kharper55/soundSteering_CAD_FINAL/Ultrasonic Sound Steering - Driver Rev. C/otherStuff/fab/UltrasonicDrive-B_Silkscreen.pdf

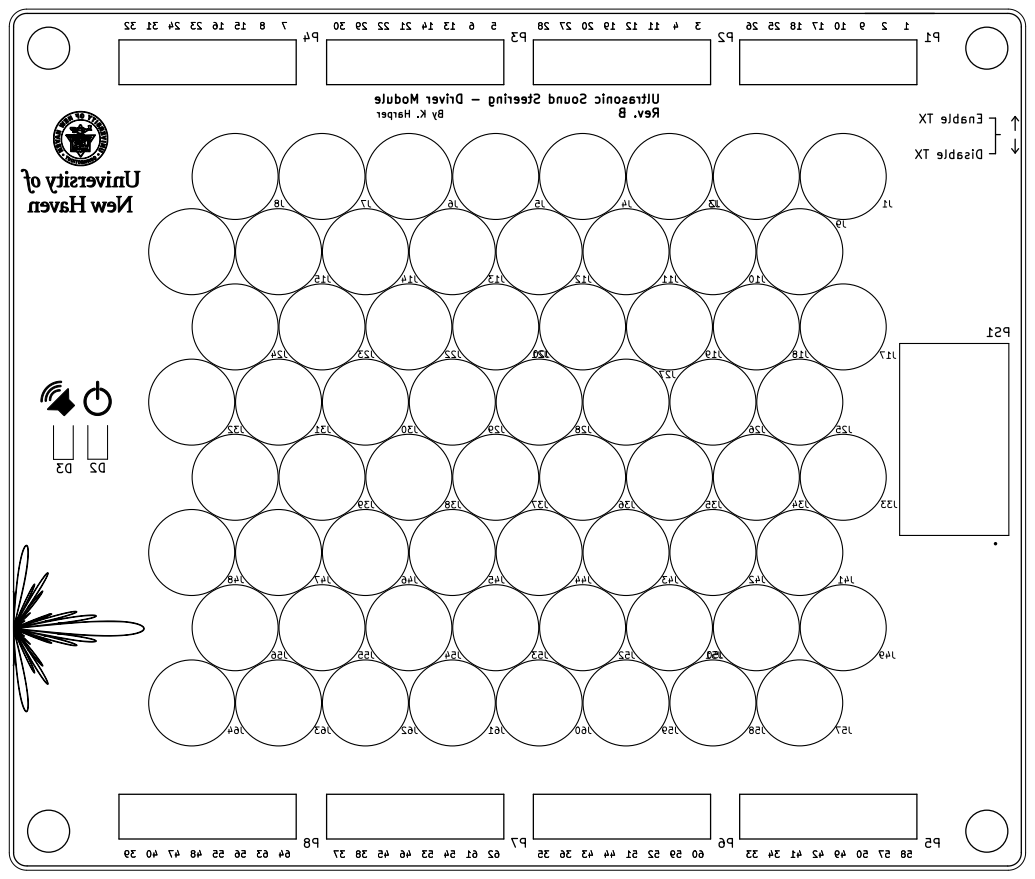
[picture p4: page 1]

15 11 By K. Harper Ultrasonic Sound Steering - Driver Module Rev. B
