kharper55/soundSteering_CAD_FINAL/Ultrasonic Sound Steering - Driver Rev. C/otherStuff/fab/UltrasonicDrive-F_Silkscreen.pdf

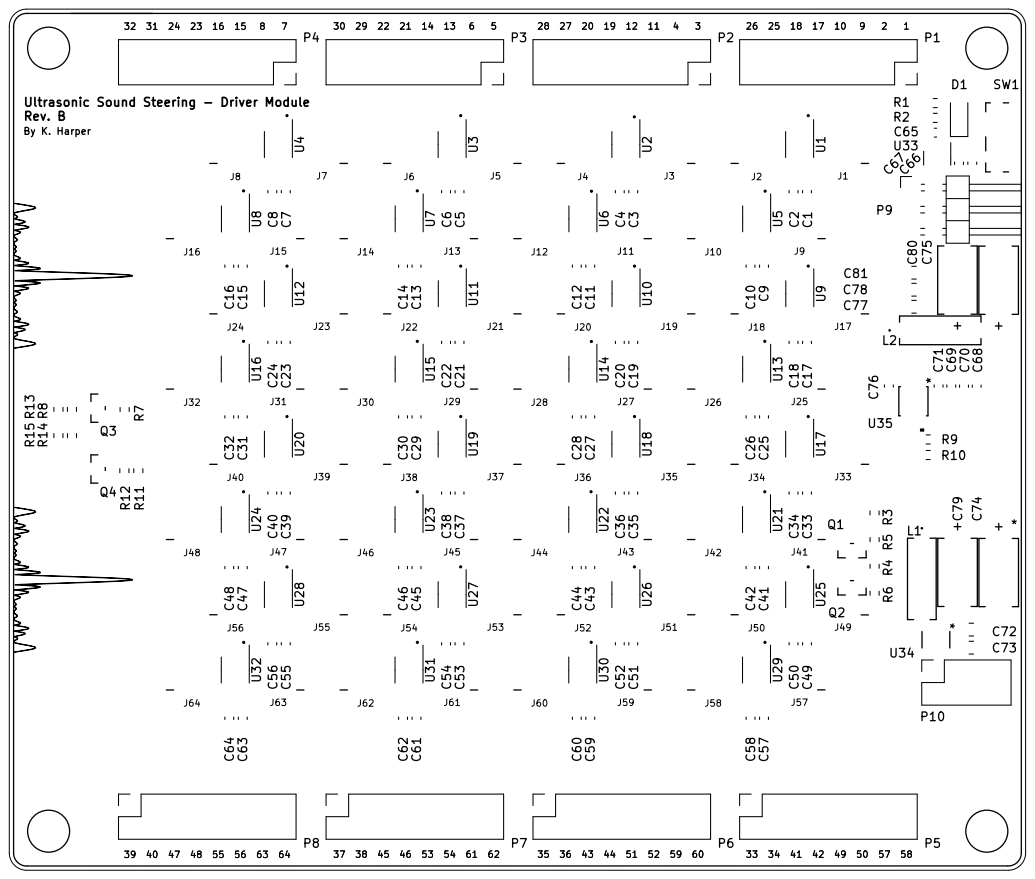
[picture p5: page 1]

30 Ultrasonic Sound Steering - Driver Module Rev. B
