kharper55/soundSteering_CAD_FINAL/Ultrasonic Sound Steering - Driver Rev. C/otherStuff/layers.pdf

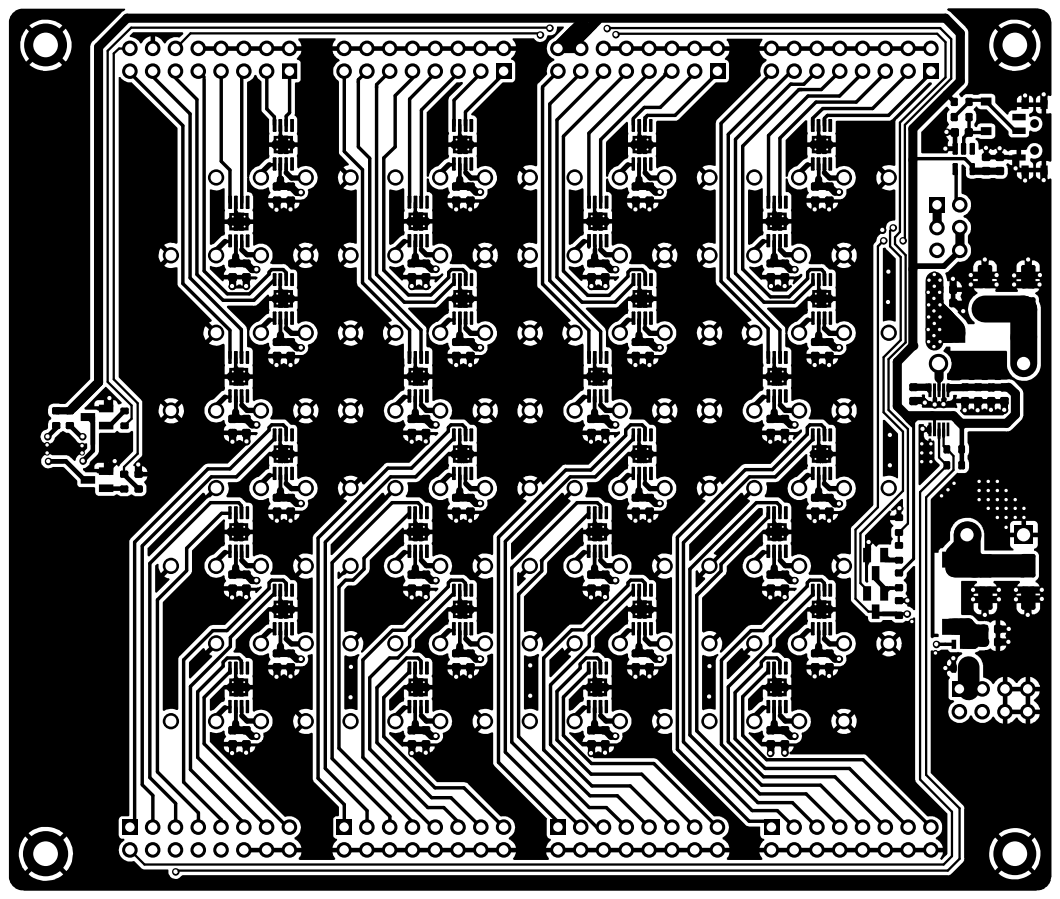
[picture p19: page 1]

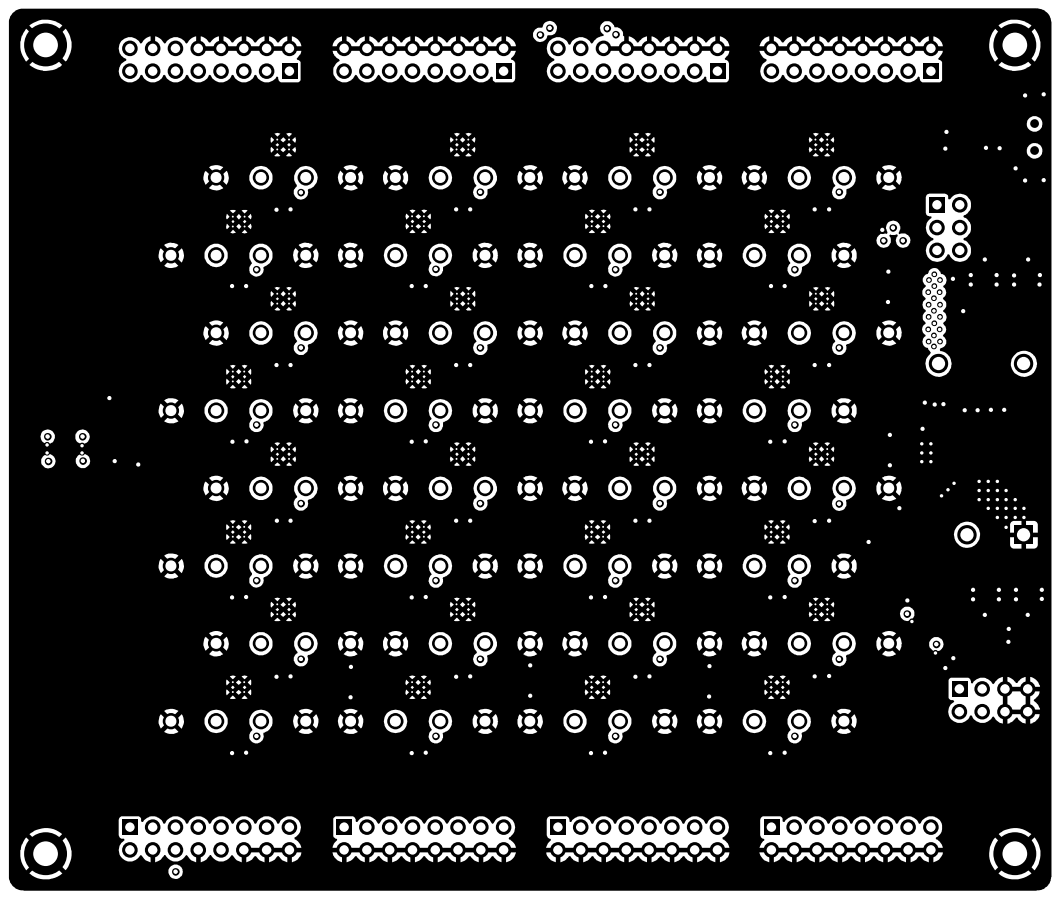
[picture p20: page 2]

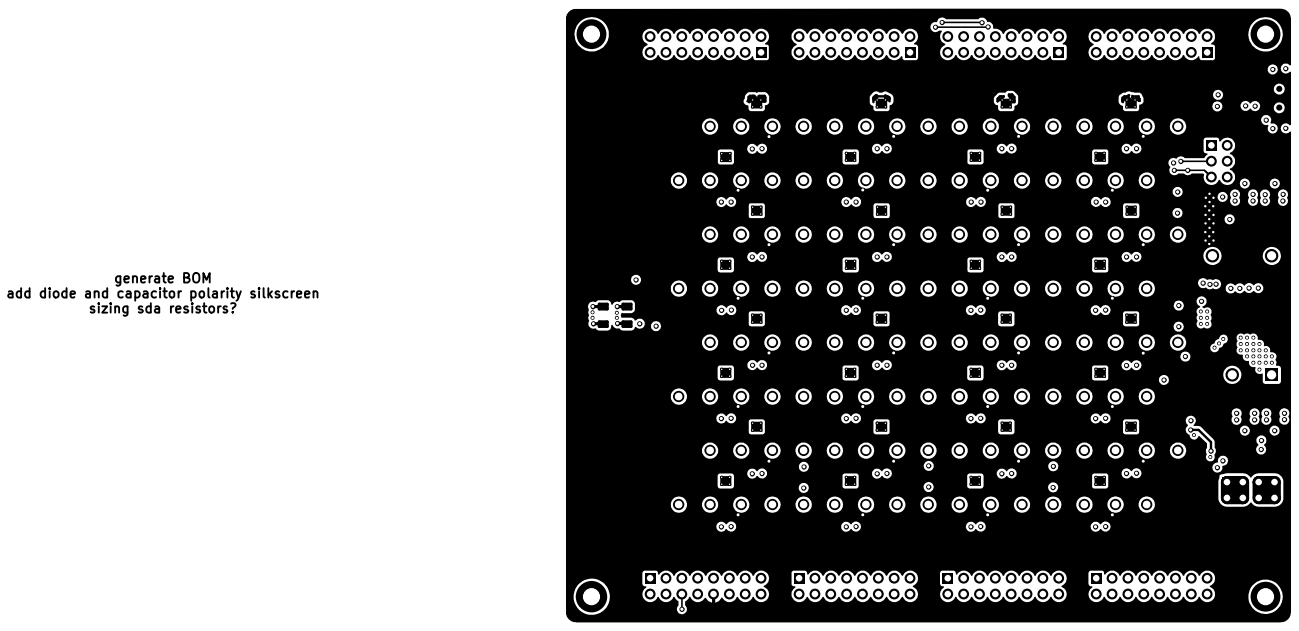
[picture p21: page 4]
