kharper55/soundSteering_CAD_FINAL/Ultrasonic Sound Steering - Remote Rev. B/otherStuff/layers.pdf

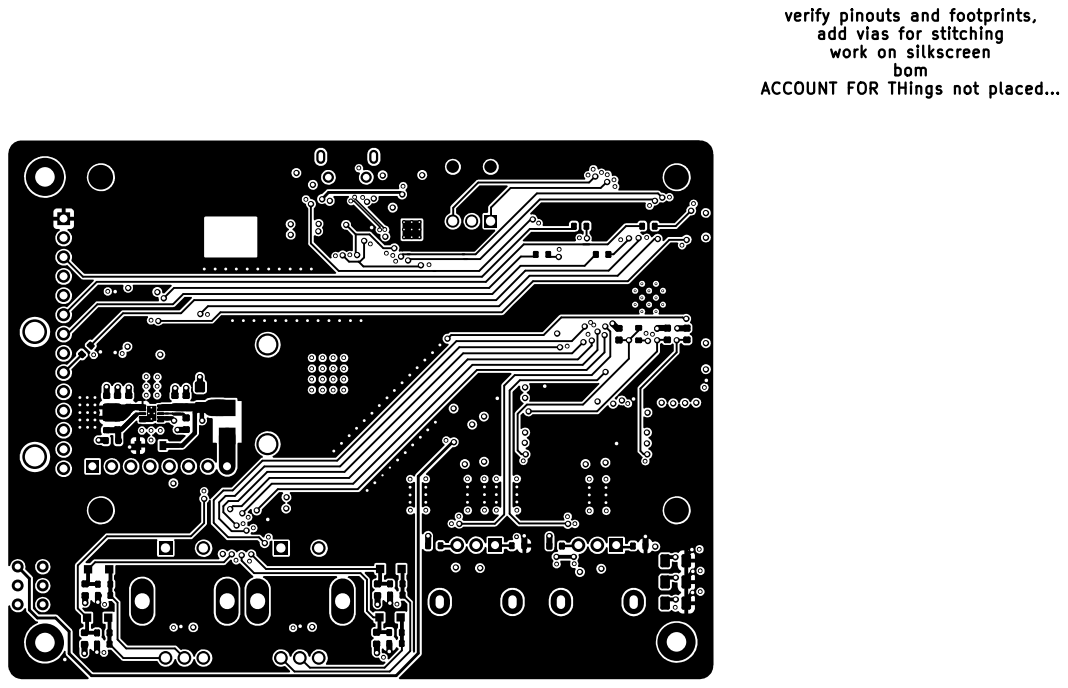
[picture p22: page 1]

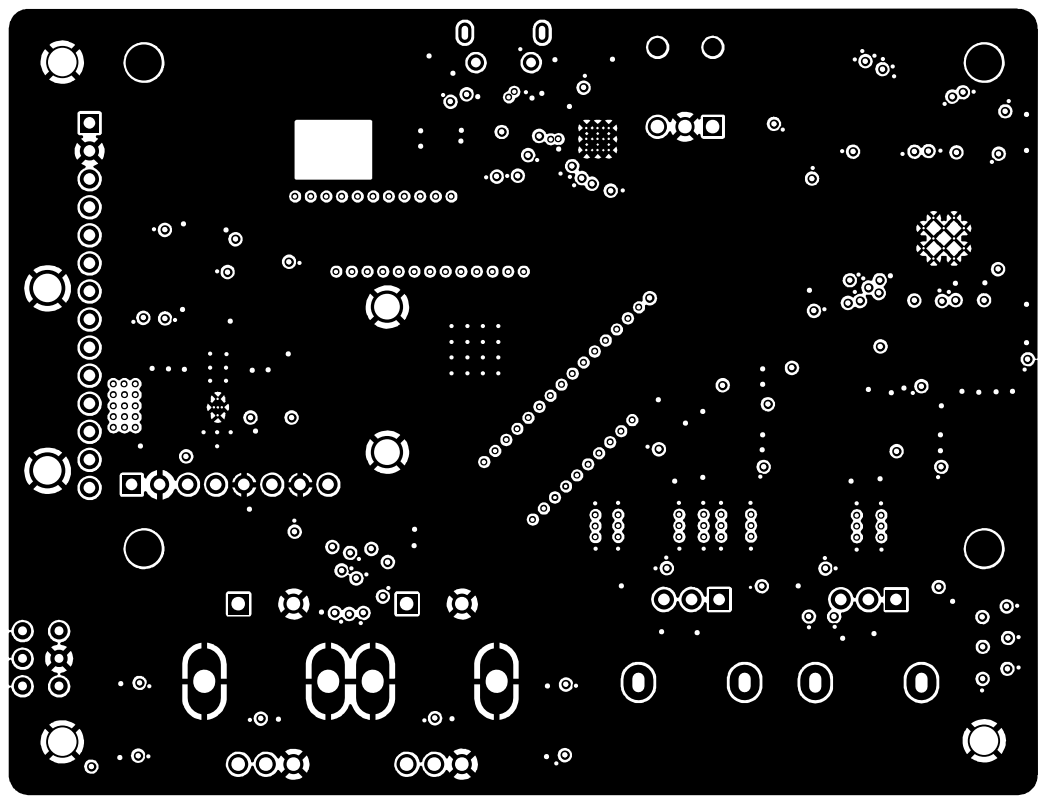
[picture p23: page 2]

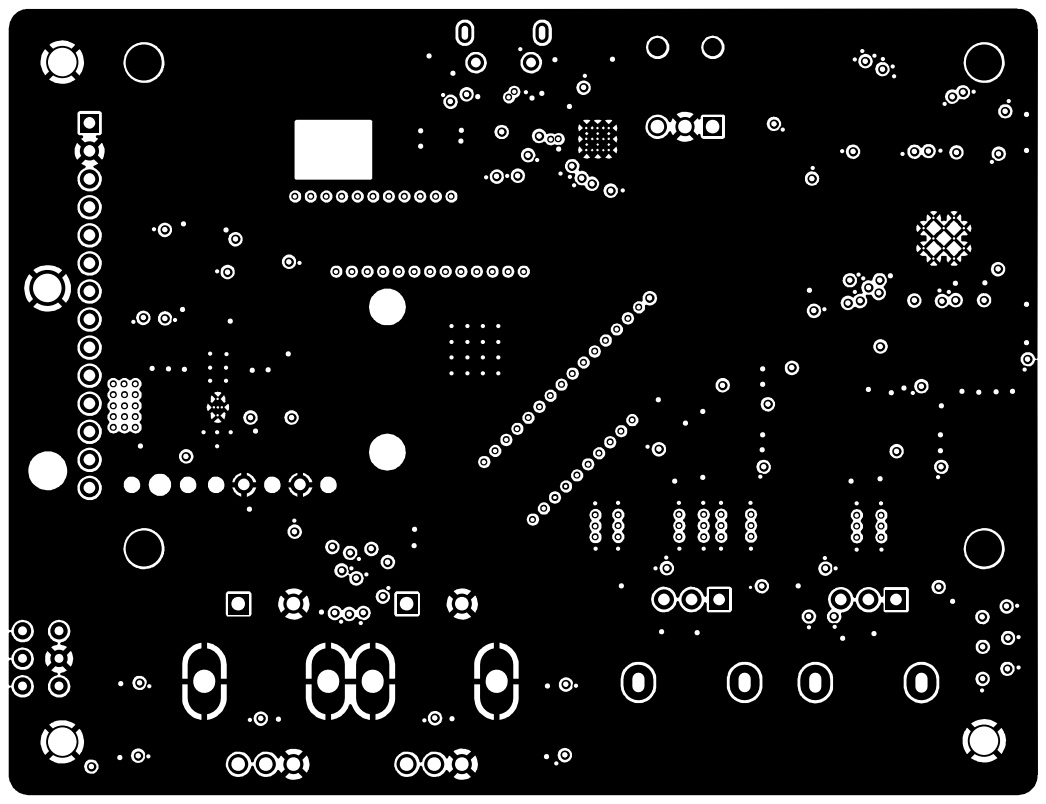
[picture p24: page 3]

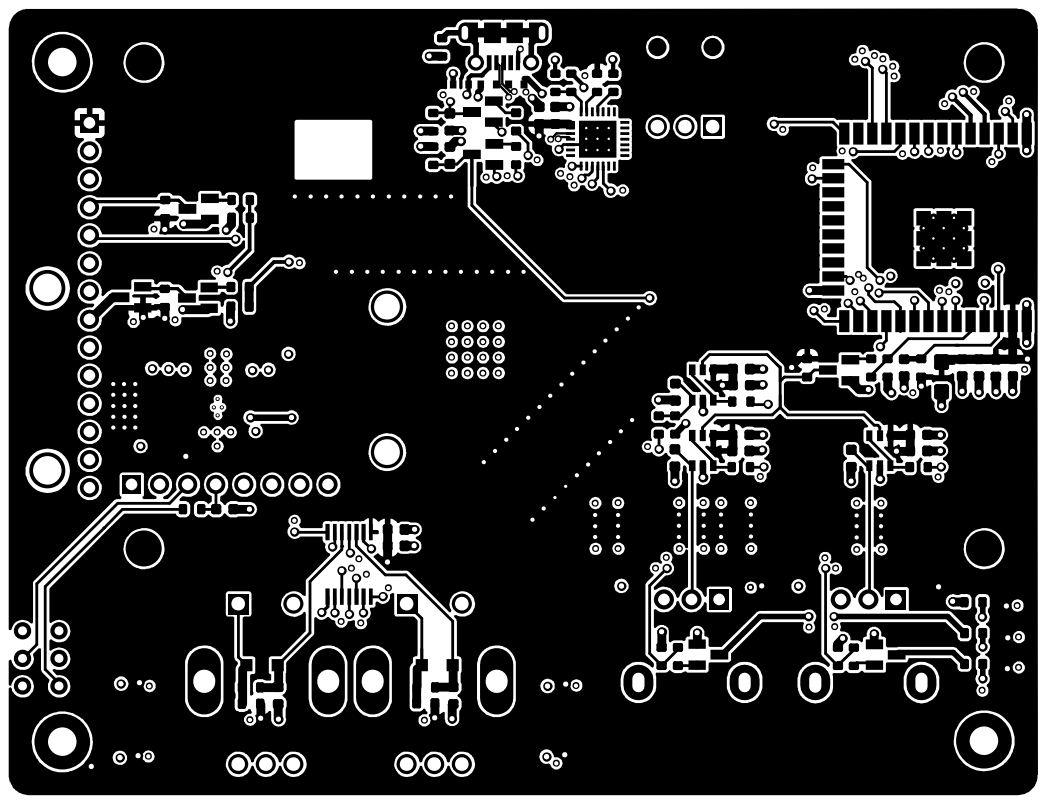
[picture p25: page 4]
