kharper55/soundSteering_CAD_FINAL/Ultrasonic Sound Steering - Driver Rev. C/otherStuff/fab/UltrasonicDrive-B_Cu.pdf

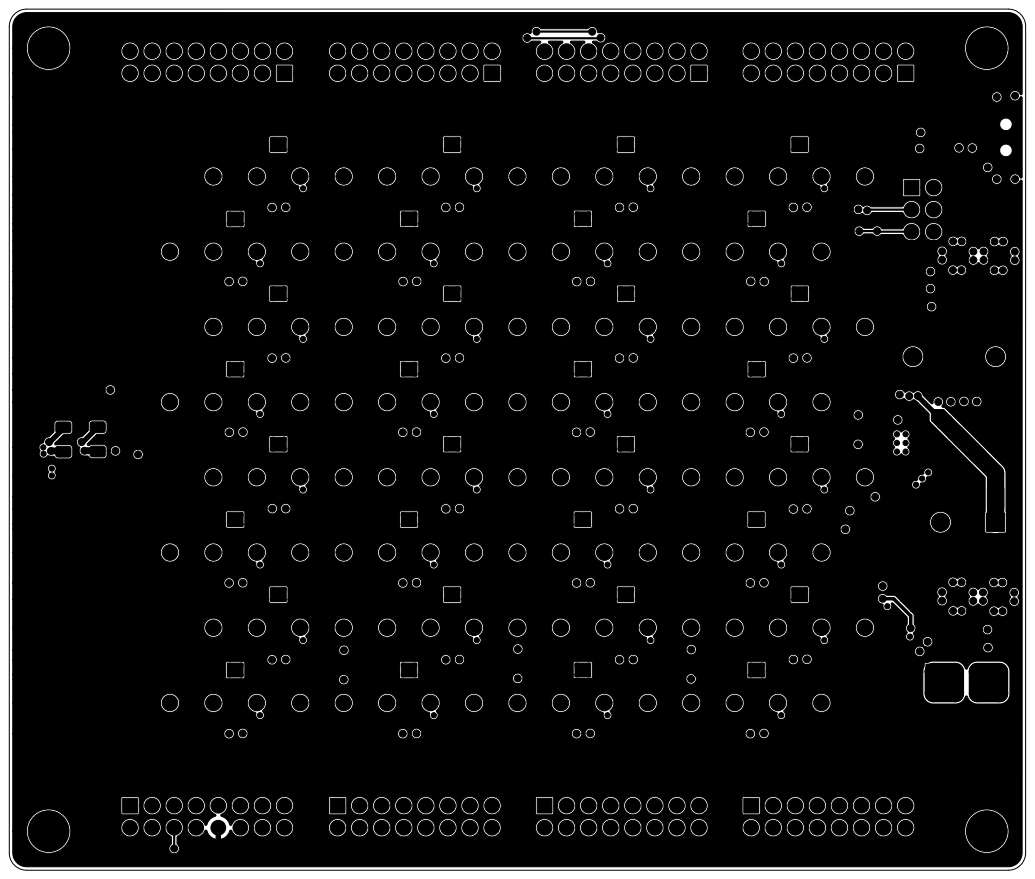
[picture p26: page 1]
