kharper55/soundSteering_CAD_FINAL/Ultrasonic Sound Steering - Driver Rev. C/otherStuff/fab/UltrasonicDrive-B_Mask.pdf

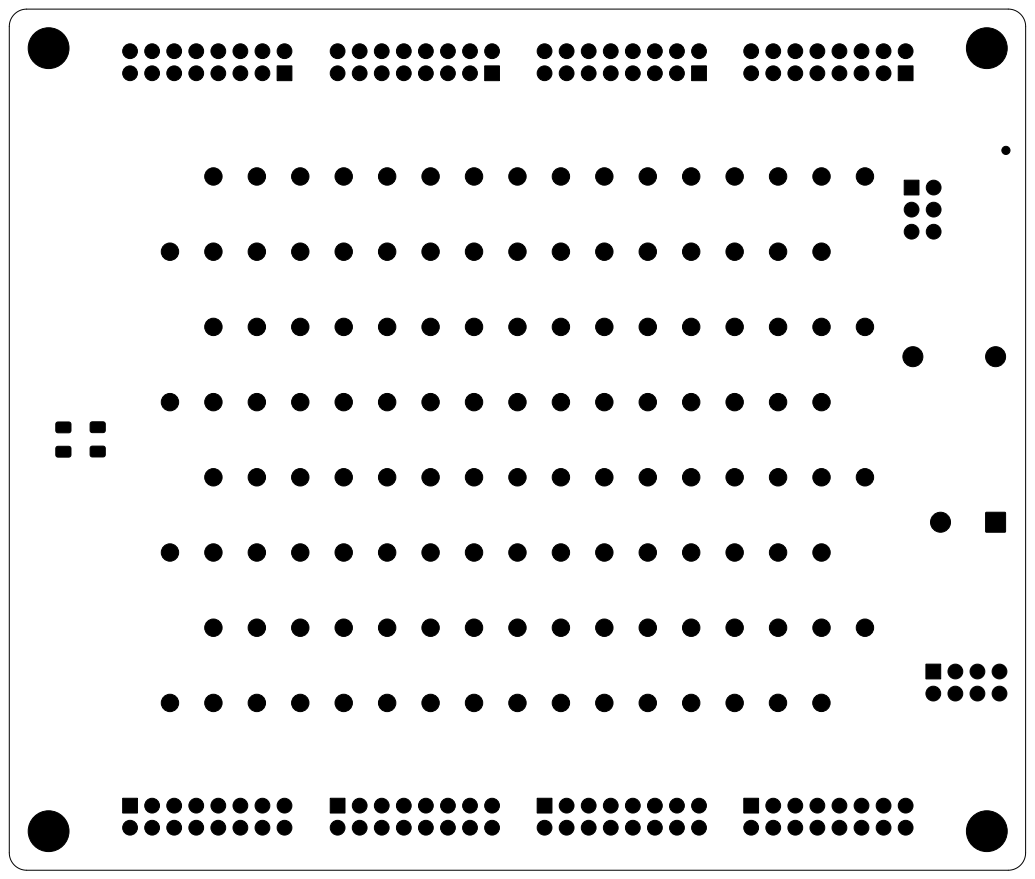
[picture p27: page 1]
