kharper55/soundSteering_CAD_FINAL/Ultrasonic Sound Steering - Driver Rev. C/otherStuff/fab/UltrasonicDrive-B_Paste.pdf

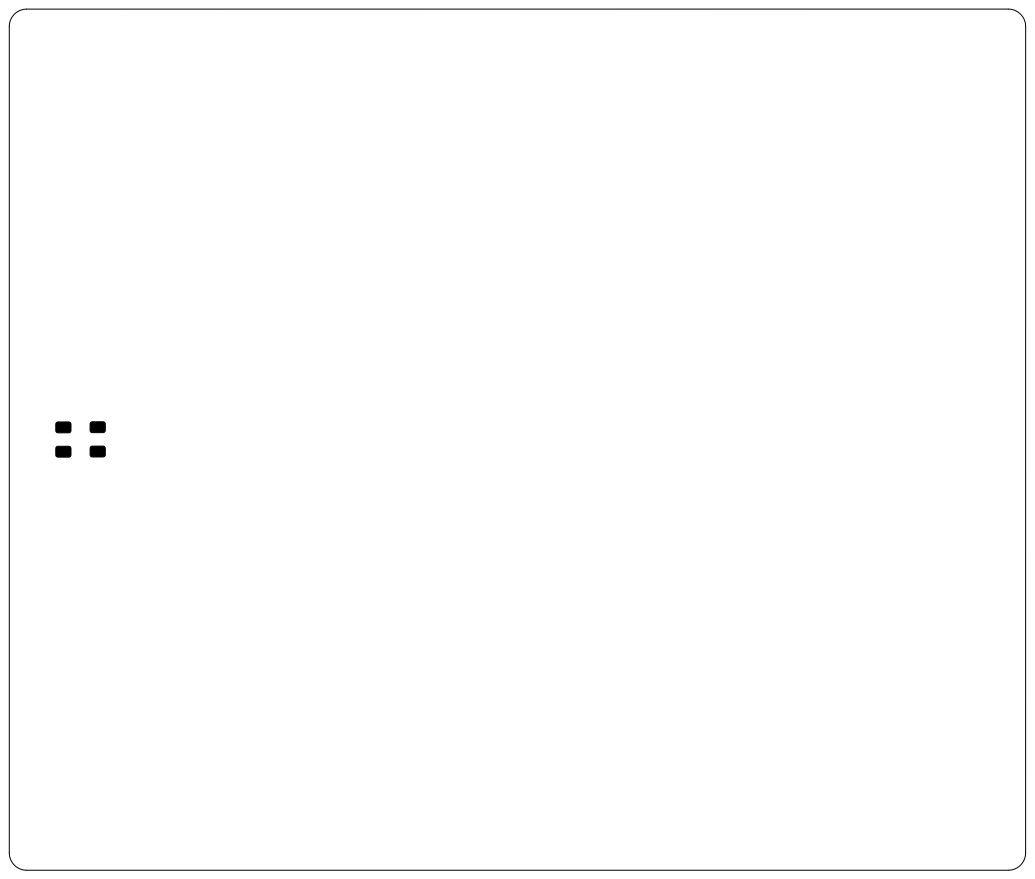
[picture p28: page 1]
