kharper55/soundSteering_CAD_FINAL/Ultrasonic Sound Steering - Control Rev. B/otherStuff/control_Analog.kicad_sch

## KiCad design Ultrasonic Sound Steering - Control Rev. B/otherStuff/control_Analog.kicad_sch (2024-05-02)

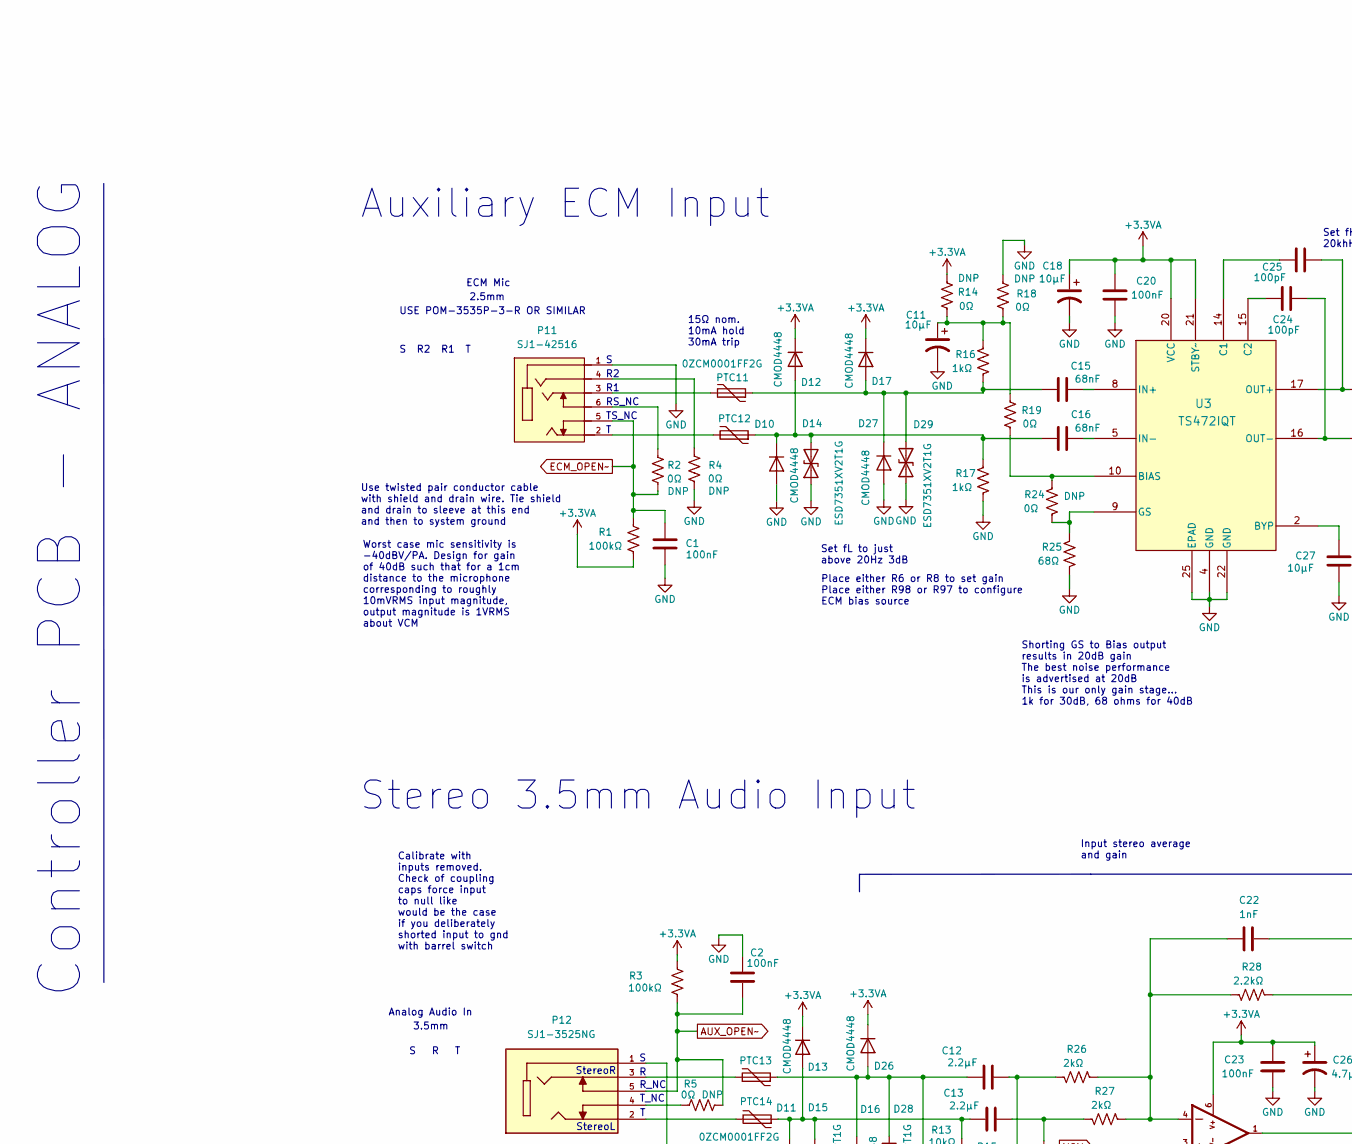
[picture p40: schematic control_Analog.kicad_sch, part in row 1, column 1]

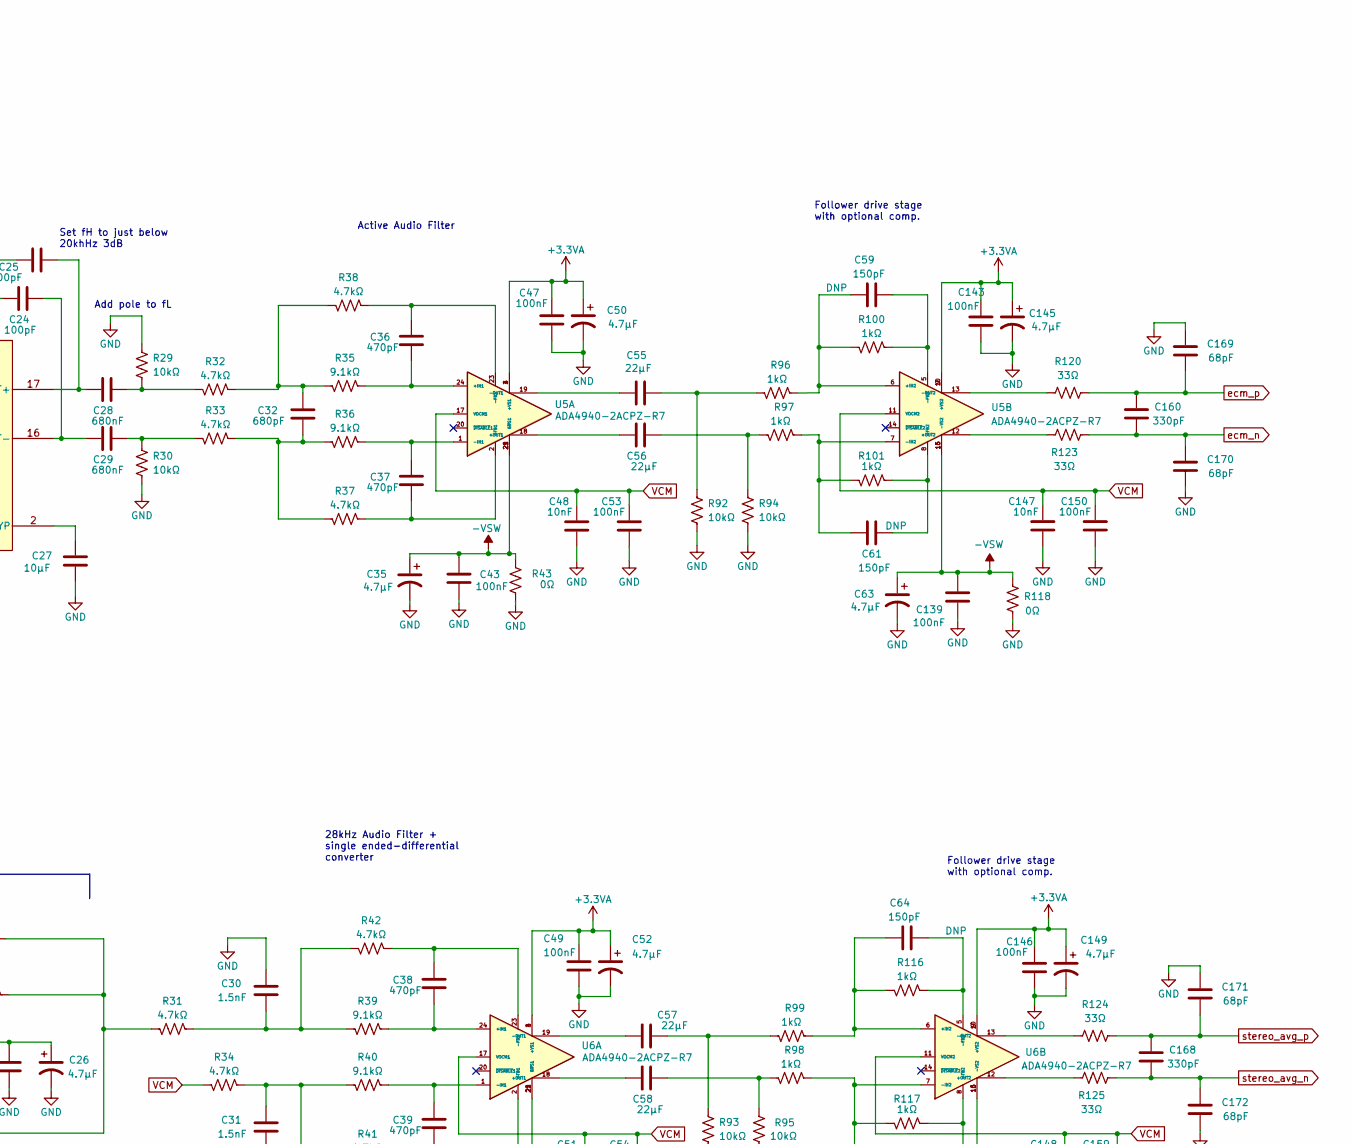
[picture p41: schematic control_Analog.kicad_sch, part in row 1, column 2]

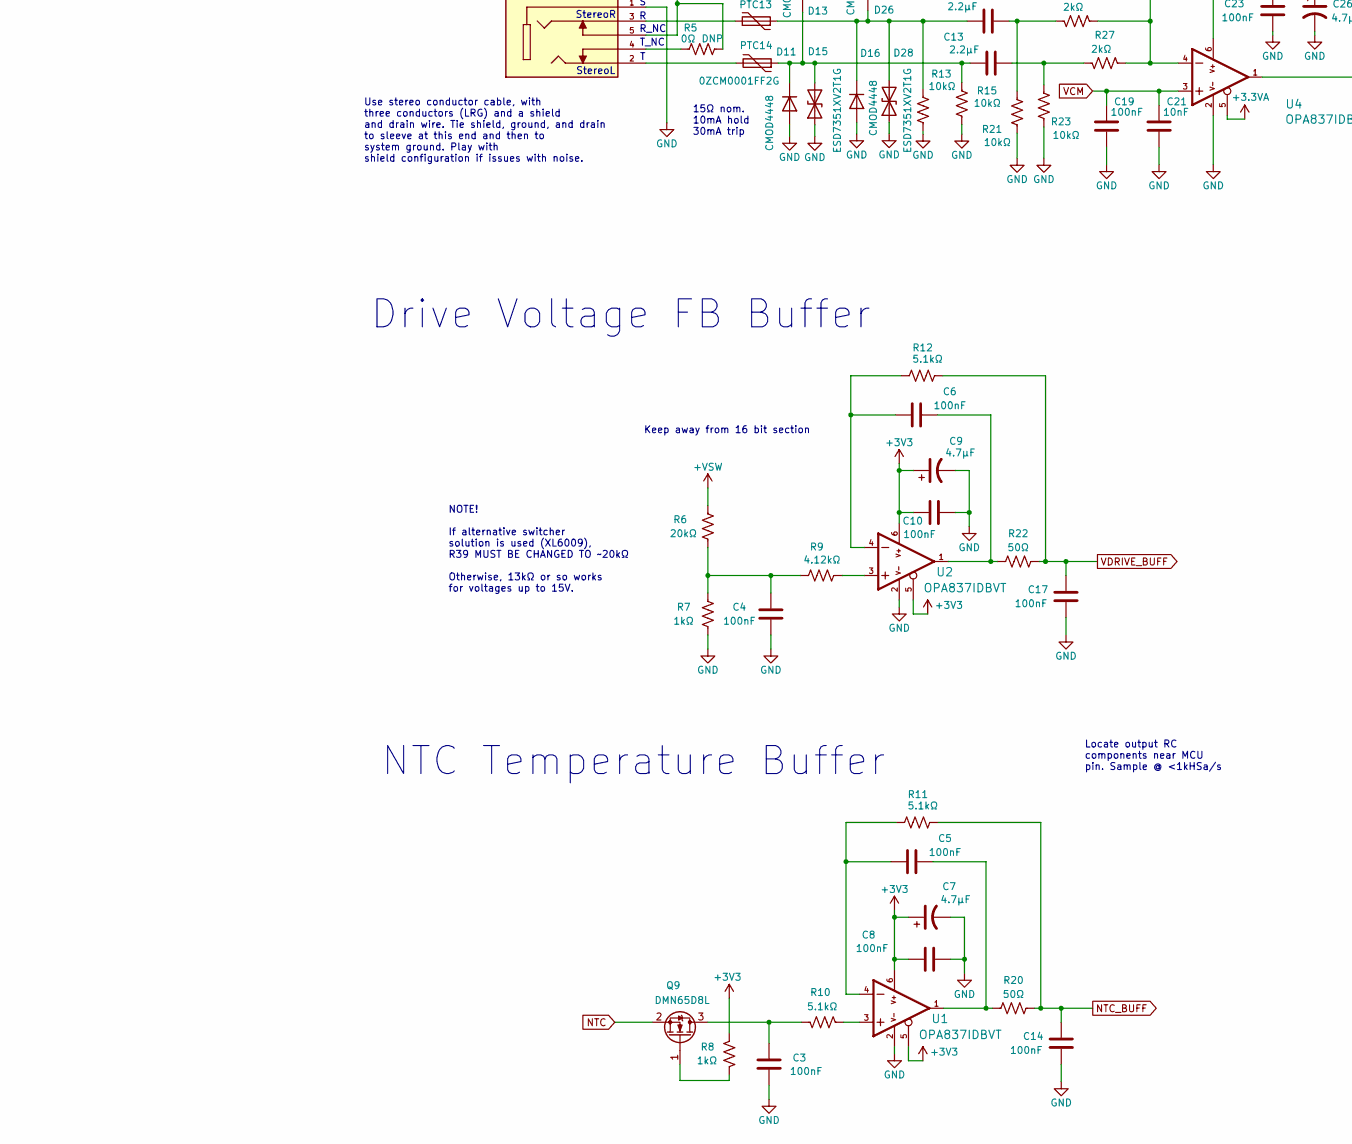
[picture p42: schematic control_Analog.kicad_sch, part in row 2, column 1]

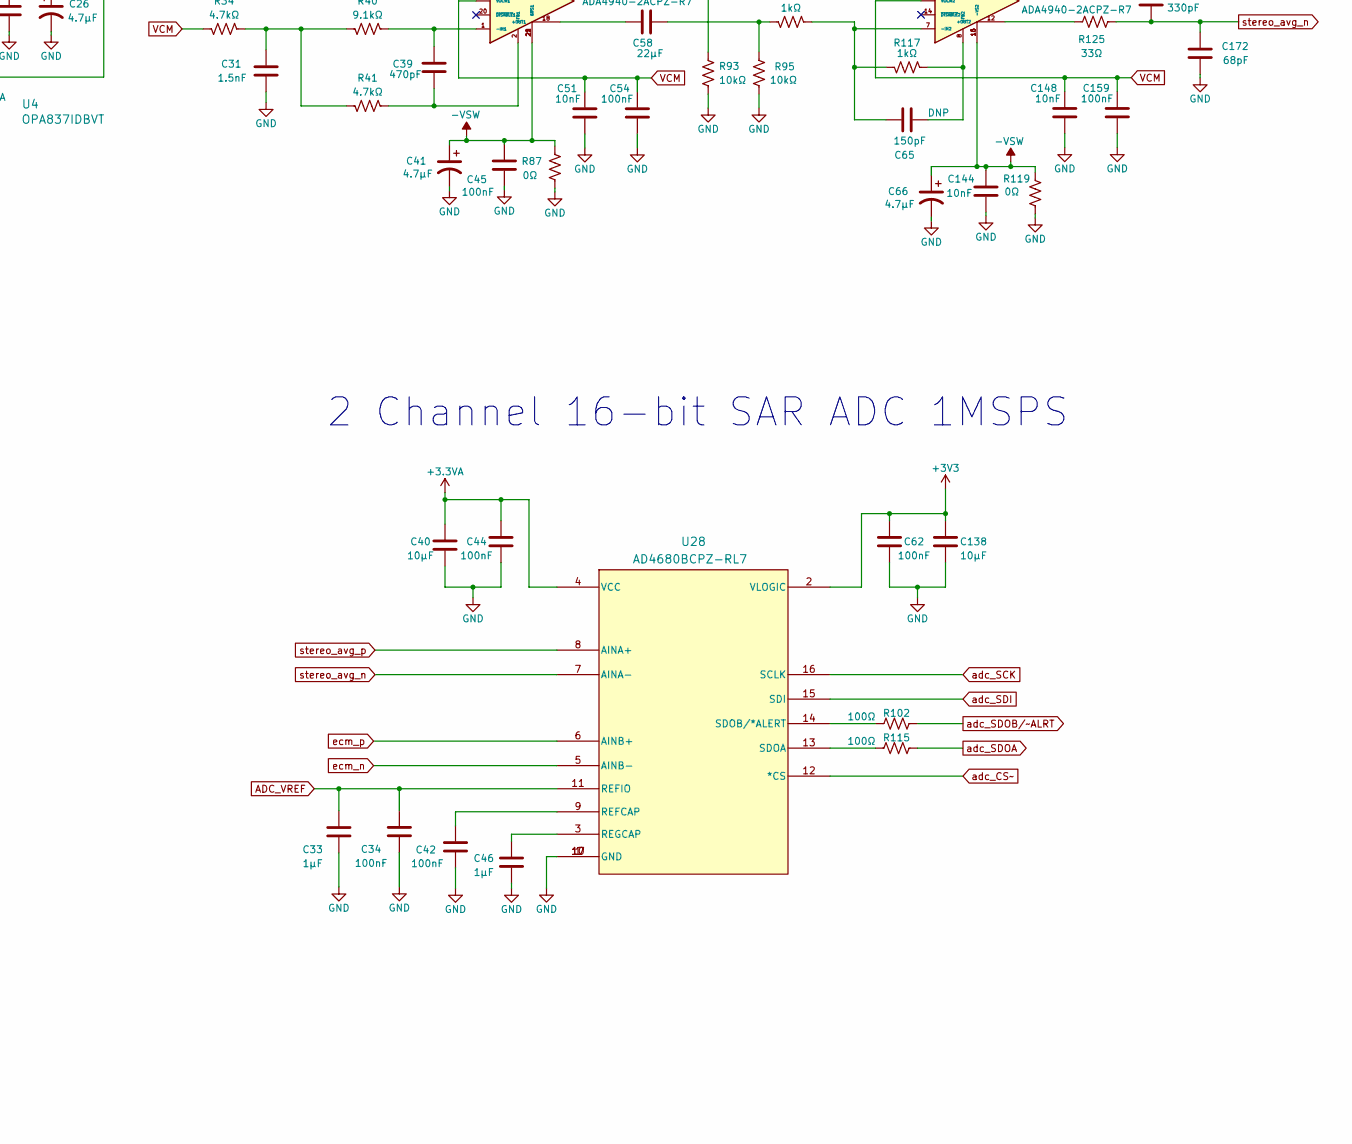
[picture p43: schematic control_Analog.kicad_sch, part in row 2, column 2]

Parts:
C1, C2, C3, C4, C5, C6, C8, C10, C14, C17, C19, C20, C23, C34, C42, C43, C44, C45, C47, C49, C53, C54, C62, C139, C143, C146, C150, C159: 100nF; C_0603
C7, C9, C26, C35, C41, C50, C52, C63, C66, C145, C149: 4.7µF; C_TANT_3216-18_Kemet-A
C11, C18: 10µF; C_TANT_3216-18_Kemet-A
C12, C13: 2.2µF; C_0603
C15, C16: 68nF; C_0603
C21, C48, C144, C147, C148: 10nF; C_0603
C22: 1nF; C_0603
C24, C25: 100pF; C_0603
C27, C40, C138: 10µF; C_0603
C28, C29: 680nF; C_0603
C30, C31: 1.5nF; C_0603
C32: 680pF; C_0603
C33, C46: 1µF; C_0603
C36, C37, C38, C39: 470pF; C_0603
C51: 10nF; C_0603_1608Metric
C55, C56, C57, C58: 22µF; C_0603
C59, C61, C64, C65: 150pF; C_0603
C160, C168: 330pF; C_0603
C169, C170, C171, C172: 68pF; C_0603
D10, D11, D12, D13, D16, D17, D26, D27: CMOD4448; D_SOD_523
D14, D15, D28, D29: ESD7351XV2T1G; D_SOD_523
P11: SJ1-42516; CUI_SJ1-42516; PART_REV 1.01
P12: SJ1-3525NG; CUI_SJ1-3525NG; PARTREV 1.01
PTC11, PTC12, PTC13, PTC14: 0ZCM0001FF2G; R_0603
Q9: DMN65D8L; T_SOT23
R1, R3: 100kΩ; R_0603
R2, R4, R5, R14, R18, R19, R24, R43, R87, R118, R119: 0Ω; R_0603
R6: 20kΩ; R_0603
R7, R8, R16, R17, R96, R97, R98, R99, R100, R101, R116, R117: 1kΩ; R_0603
R9: 4.12kΩ; R_0603
R10, R11, R12: 5.1kΩ; R_0603
R13, R15, R21, R23, R29, R30, R92, R93, R94, R95: 10kΩ; R_0603
R20, R22: 50Ω; R_0603
R25: 68Ω; R_0603
R26, R27: 2kΩ; R_0603
R28: 2.2kΩ; R_0603
R31, R32, R33, R34, R37, R38, R41, R42: 4.7kΩ; R_0603
R35, R36, R39, R40: 9.1kΩ; R_0603
R102, R115: 100Ω; R_0603
R120, R123, R124, R125: 33Ω; R_0603
U1, U2, U4: OPA837IDBVT; IC_SOT23-6
U3: TS472IQT; IC_QFN-24_EP_4X4
U5, U6: ADA4940-2ACPZ-R7; IC_QFN-24_LFCSP_EP_4X4; PARTREV E
U28: AD4680BCPZ-RL7; IC_QFN-16_LFCSP_EP_3X3

Connections:
+3.3VA: C18.1, C20.1, C23.1, C26.1, C40.2, C44.2, C47.1, C49.1, C50.1, C52.1, C143.1, C145.1, C146.1, C149.1, D12.1 (K), D13.1 (K), D17.1 (K), D26.1 (K), R1.1, R3.2, R14.2, U3.20 (VCC), U3.21 (STBY~), U4.5, U4.6, U5.3 (+VS1), U5.4 (+VS1), U5.9 (+VS2), U5.10 (+VS2), U6.3 (+VS1), U6.4 (+VS1), U6.9 (+VS2), U6.10 (+VS2), U28.4 (VCC)
+3V3: C7.1, C8.1, C9.1, C10.1, C62.2, C138.2, R8.1, U1.5, U1.6, U2.5, U2.6, U28.2 (VLOGIC)
+VSW: R6.1
-VSW: C35.1, C41.1, C43.1, C45.1, C63.1, C66.1, C139.1, C144.1, R43.1, R87.1, R118.1, R119.1, U5.15 (−VS2), U5.16 (−VS2), U5.21 (−VS1), U5.22 (−VS1), U5.25 (EP), U6.15 (−VS2), U6.16 (−VS2), U6.21 (−VS1), U6.22 (−VS1), U6.25 (EP)
ADC_VREF: C33.2, C34.2, U28.11 (REFIO)
AUX_OPEN~: C2.2, P12.5, R3.1, R5.1
ECM_OPEN~: C1.1, P11.5, R1.2, R2.1
GND: C1.2, C2.1, C3.1, C4.1, C7.2, C8.2, C9.2, C10.2, C11.2, C14.1, C17.1, C18.2, C19.2, C20.2, C21.2, C23.2, C26.2, C27.1, C30.1, C31.2, C33.1, C34.1, C35.2, C40.1, C41.2, C42.1, C43.2, C44.1, C45.2, C46.1, C47.2, C48.2, C49.2, C50.2, C51.2, C52.2, C53.2, C54.2, C62.1, C63.2, C66.2, C138.1, C139.2, C143.2, C144.2, C145.2, C146.2, C147.2, C148.2, C149.2, C150.2, C159.2, C169.2, C170.1, C171.2, C172.1, D10.2 (A), D11.2 (A), D14.1 (A1), D15.1 (A1), D16.2 (A), D27.2 (A), D28.1 (A1), D29.1 (A1), P11.1, P12.1, R4.1, R7.2, R13.1, R15.1, R17.1, R18.2, R21.1, R23.1, R25.1, R29.2, R30.1, R43.2, R87.2, R92.1, R93.1, R94.1, R95.1, R118.2, R119.2, U1.2, U2.2, U3.4 (GND), U3.22 (GND), U3.25 (EPAD), U4.2, U28.1 (GND), U28.10 (GND), U28.17 (GND)
NTC: Q9.2 (S)
NTC_BUFF: C14.2, R11.2, R20.2
unnamed: C3.2, Q9.3 (D), R10.2
unnamed: C4.2, R6.2, R7.1, R9.1
unnamed: C5.1, R20.1, U1.1
unnamed: C5.2, R11.1, U1.4
unnamed: C6.1, R22.1, U2.1
unnamed: C6.2, R12.1, U2.4
unnamed: C11.1, R14.1, R16.2, R18.1, R19.2
unnamed: C12.1, D16.1 (K), D26.2 (A), D28.2 (A2), PTC13.1, R13.2
unnamed: C12.2, R21.2, R26.2
unnamed: C13.1, D11.1 (K), D13.2 (A), D15.2 (A2), PTC14.1, R15.2
unnamed: C13.2, R23.2, R27.2
unnamed: C15.1, D17.2 (A), D27.1 (K), D29.2 (A2), PTC11.1, R16.1
unnamed: C15.2, U3.8 (IN+)
unnamed: C16.1, D10.1 (K), D12.2 (A), D14.2 (A2), PTC12.1, R17.2
unnamed: C16.2, U3.5 (IN-)
unnamed: C22.1, R26.1, R27.1, R28.2, U4.4
unnamed: C22.2, R28.1, R31.1, U4.1
unnamed: C24.1, U3.15 (C2)
unnamed: C24.2, C29.1, U3.16 (OUT-)
unnamed: C25.1, U3.14 (C1)
unnamed: C25.2, C28.1, U3.17 (OUT+)
unnamed: C27.2, U3.2 (BYP)
unnamed: C28.2, R29.1, R32.1
unnamed: C29.2, R30.2, R33.1
unnamed: C30.2, R31.2, R39.1, R42.1
unnamed: C31.1, R34.2, R40.1, R41.1
unnamed: C32.1, R33.2, R36.1, R37.1
unnamed: C32.2, R32.2, R35.1, R38.1
unnamed: C36.1, R38.2, U5.23 (-FB1)
unnamed: C36.2, R35.2, U5.24 (+IN1)
unnamed: C37.1, R36.2, U5.1 (-IN1)
unnamed: C37.2, R37.2, U5.2 (+FB1)
unnamed: C38.1, R42.2, U6.23 (-FB1)
unnamed: C38.2, R39.2, U6.24 (+IN1)
unnamed: C39.1, R40.2, U6.1 (-IN1)
unnamed: C39.2, R41.2, U6.2 (+FB1)
unnamed: C42.2, U28.9 (REFCAP)
unnamed: C46.2, U28.3 (REGCAP)
unnamed: C55.1, U5.19 (-OUT1)
unnamed: C55.2, R92.2, R96.2
unnamed: C56.1, U5.18 (+OUT1)
unnamed: C56.2, R94.2, R97.2
unnamed: C57.1, U6.19 (-OUT1)
unnamed: C57.2, R93.2, R99.2
unnamed: C58.1, U6.18 (+OUT1)
unnamed: C58.2, R95.2, R98.2
unnamed: C59.1, R96.1, R100.2, U5.6 (+IN2)
unnamed: C59.2, R100.1, U5.5 (-FB2)
unnamed: C61.1, R101.2, U5.8 (+FB2)
unnamed: C61.2, R97.1, R101.1, U5.7 (-IN2)
unnamed: C64.1, R99.1, R116.2, U6.6 (+IN2)
unnamed: C64.2, R116.1, U6.5 (-FB2)
unnamed: C65.1, R117.2, U6.8 (+FB2)
unnamed: C65.2, R98.1, R117.1, U6.7 (-IN2)
unnamed: P11.2, PTC12.2
unnamed: P11.3, PTC11.2
unnamed: P11.4, R4.2
unnamed: P11.6, R2.2
unnamed: P12.2, PTC14.2
unnamed: P12.3, PTC13.2
unnamed: P12.4, R5.2
unnamed: Q9.1 (G), R8.2
unnamed: R9.2, U2.3
unnamed: R10.1, U1.3
unnamed: R19.1, R24.2, U3.10 (BIAS)
unnamed: R24.1, R25.2, U3.9 (GS)
unnamed: R102.1, U28.14 (SDOB/*ALERT)
unnamed: R115.1, U28.13 (SDOA)
unnamed: R120.2, U5.13 (-OUT2)
unnamed: R123.2, U5.12 (+OUT2)
unnamed: R124.2, U6.13 (-OUT2)
unnamed: R125.2, U6.12 (+OUT2)
unnamed: U3.1 (NC), U3.3 (NC), U3.6 (NC), U3.7 (NC), U3.11 (NC), U3.12 (NC), U3.13 (NC), U3.18 (NC), U3.19 (NC), U3.23 (NC), U3.24 (NC)
VCM: C19.1, C21.1, C48.1, C51.1, C53.1, C54.1, C147.1, C148.1, C150.1, C159.1, R34.1, U4.3, U5.11 (VOCM2), U5.17 (VOCM1), U6.11 (VOCM2), U6.17 (VOCM1)
VDRIVE_BUFF: C17.2, R12.2, R22.2
adc_CS~: U28.12 (*CS)
adc_SCK: U28.16 (SCLK)
adc_SDI: U28.15 (SDI)
adc_SDOA: R115.2
adc_SDOB/~ALRT: R102.2
ecm_n: C160.1, C170.2, R123.1, U28.5 (AINB-)
ecm_p: C160.2, C169.1, R120.1, U28.6 (AINB+)
stereo_avg_n: C168.1, C172.2, R125.1, U28.7 (AINA-)
stereo_avg_p: C168.2, C171.1, R124.1, U28.8 (AINA+)

Notes on the sheet:
S R T
Add pole to fL
NTC Temperature Buffer
TS_NC
Controller PCB - ANALOG
15Ω nom. 10mA hold 30mA trip
Place either R6 or R8 to set gain Place either R98 or R97 to configure ECM bias source
Auxiliary ECM Input
Use twisted pair conductor cable with shield and drain wire. Tie shield and drain to sleeve at this end and then to system ground
2 Channel 16-bit SAR ADC 1MSPS
Use stereo conductor cable, with three conductors (LRG) and a shield and drain wire. Tie shield, ground, and drain to sleeve at this end and then to system ground. Play with shield configuration if issues with noise.
Analog Audio In
StereoL
Follower drive stage with optional comp.
Locate output RC components near MCU pin. Sample @ <1kHSa/s
ECM Mic
Shorting GS to Bias output results in 20dB gain The best noise performance is advertised at 20dB This is our only gain stage... 1k for 30dB, 68 ohms for 40dB
RS_NC
StereoR
28kHz Audio Filter + single ended-differential converter
Set fH to just below 20khHz 3dB
USE POM-3535P-3-R OR SIMILAR
Stereo 3.5mm Audio Input
Drive Voltage FB Buffer
Active Audio Filter
Set fL to just above 20Hz 3dB
S R2 R1 T
2.5mm
NOTE! If alternative switcher solution is used (XL6009), R39 MUST BE CHANGED TO ~20kΩ Otherwise, 13kΩ or so works for voltages up to 15V.
3.5mm
Input stereo average and gain
Keep away from 16 bit section
R_NC
Worst case mic sensitivity is -40dBV/PA. Design for gain of 40dB such that for a 1cm distance to the microphone corresponding to roughly 10mVRMS input magnitude, output magnitude is 1VRMS about VCM
Calibrate with inputs removed. Check of coupling caps force input to null like would be the case if you deliberately shorted input to gnd with barrel switch
T_NC
