kharper55/soundSteering_CAD_FINAL/Ultrasonic Sound Steering - Control Rev. B/otherStuff/control_Digital.kicad_sch

## KiCad design Ultrasonic Sound Steering - Control Rev. B/otherStuff/control_Digital.kicad_sch (2024-05-02)

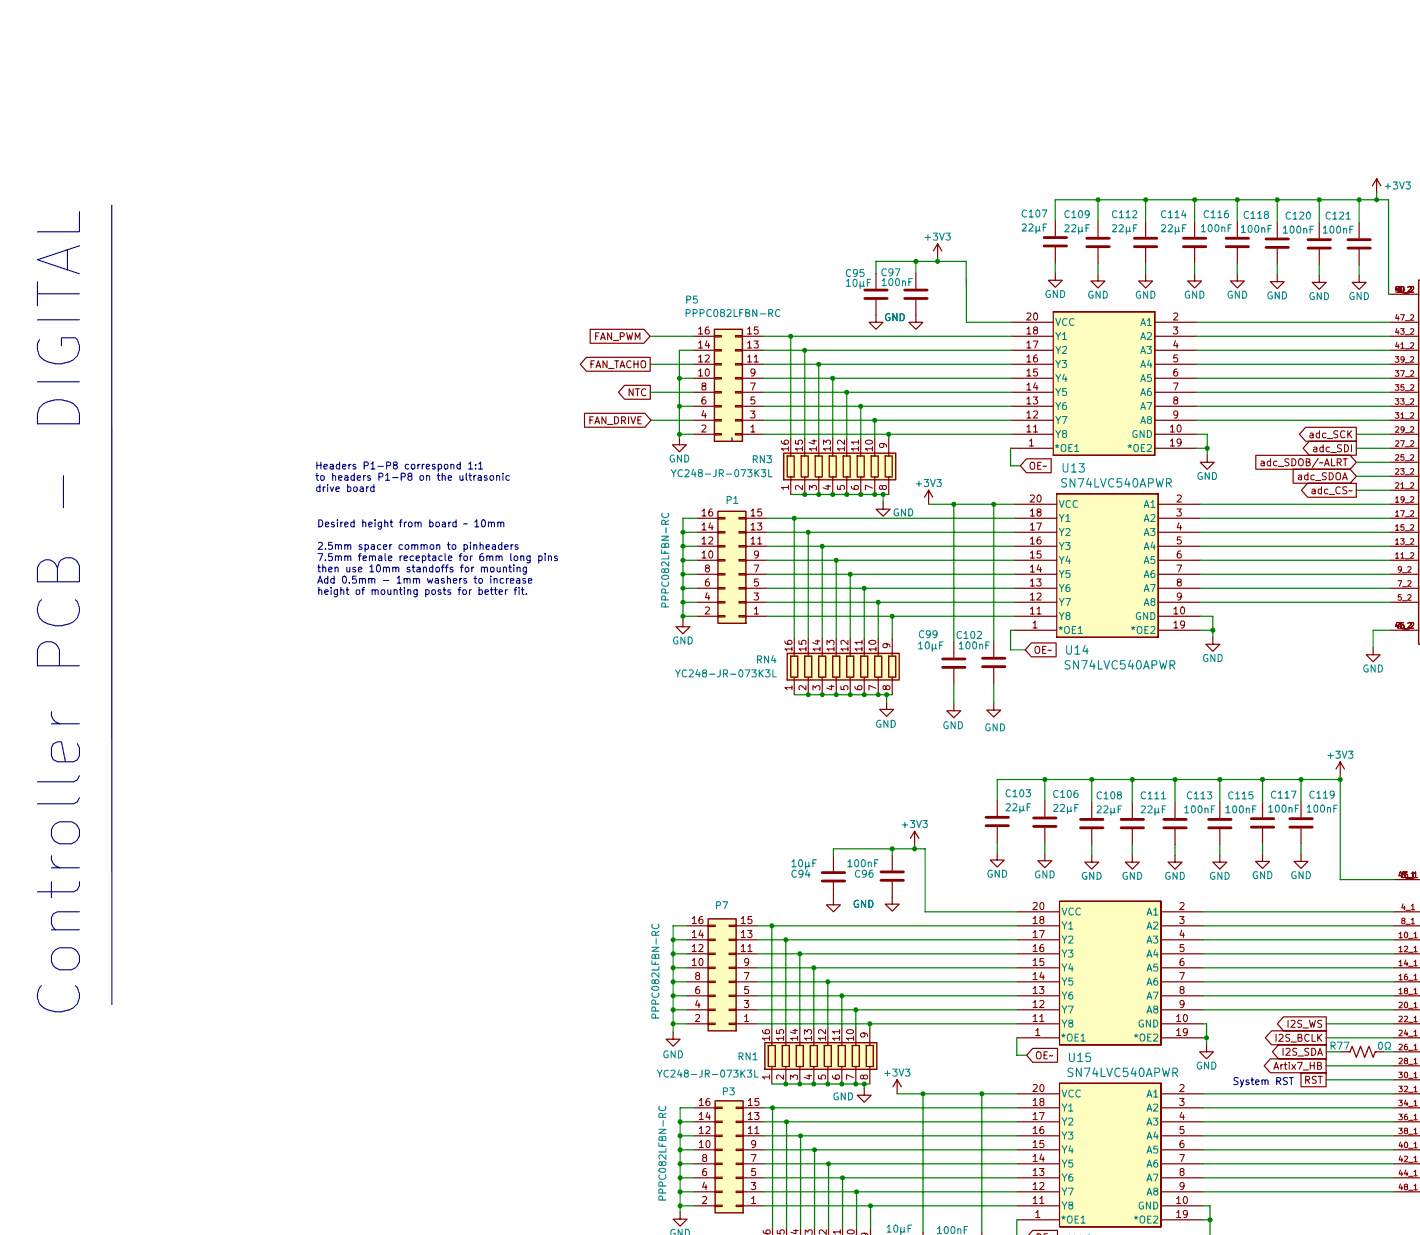
[picture p44: schematic control_Digital.kicad_sch, part in row 1, column 1]

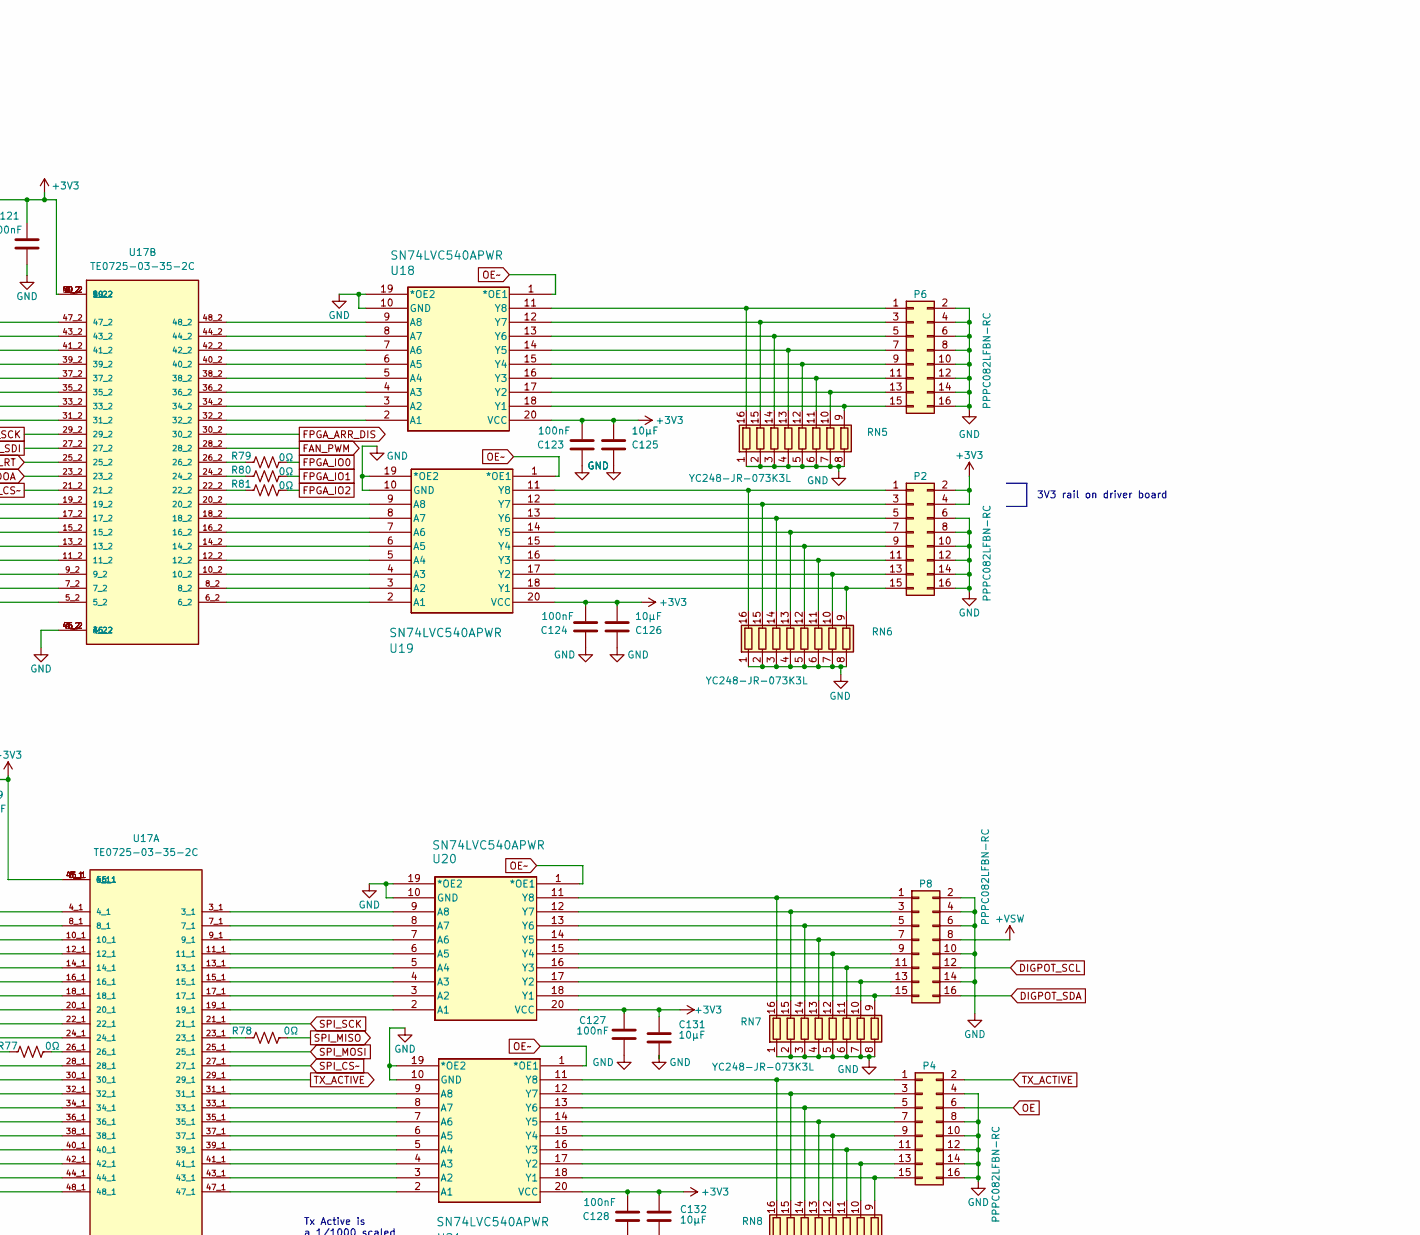
[picture p45: schematic control_Digital.kicad_sch, part in row 1, column 2]

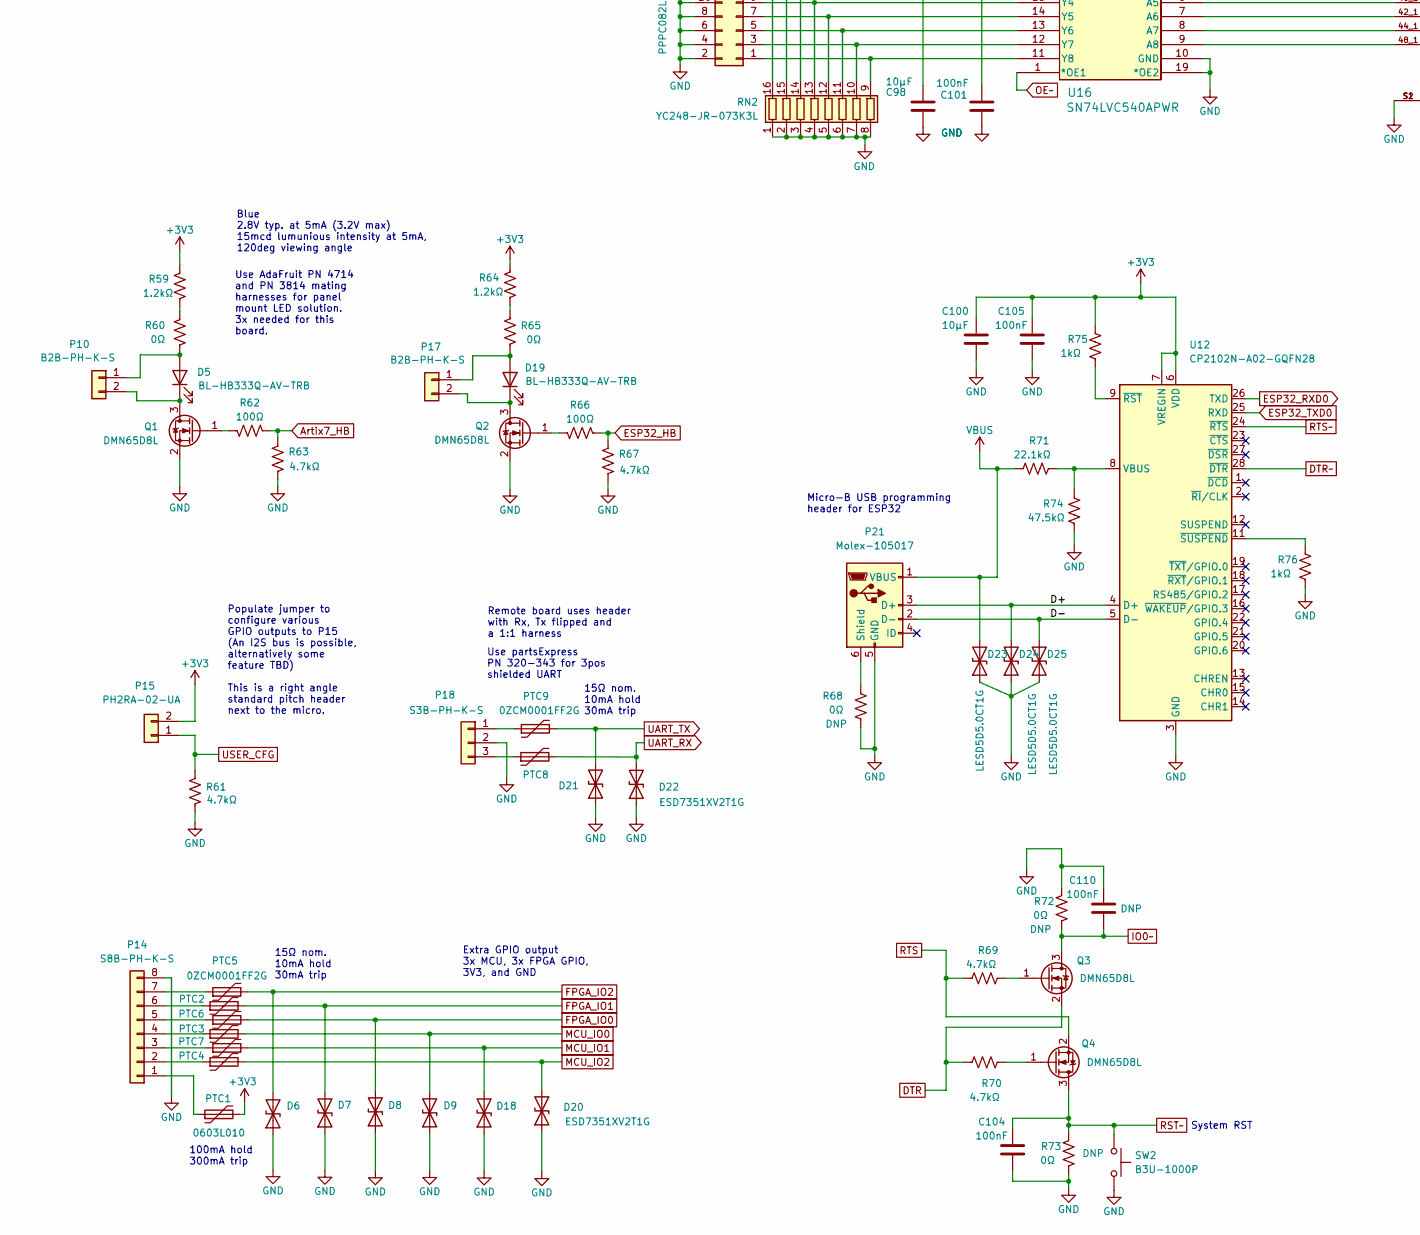
[picture p46: schematic control_Digital.kicad_sch, part in row 2, column 1]

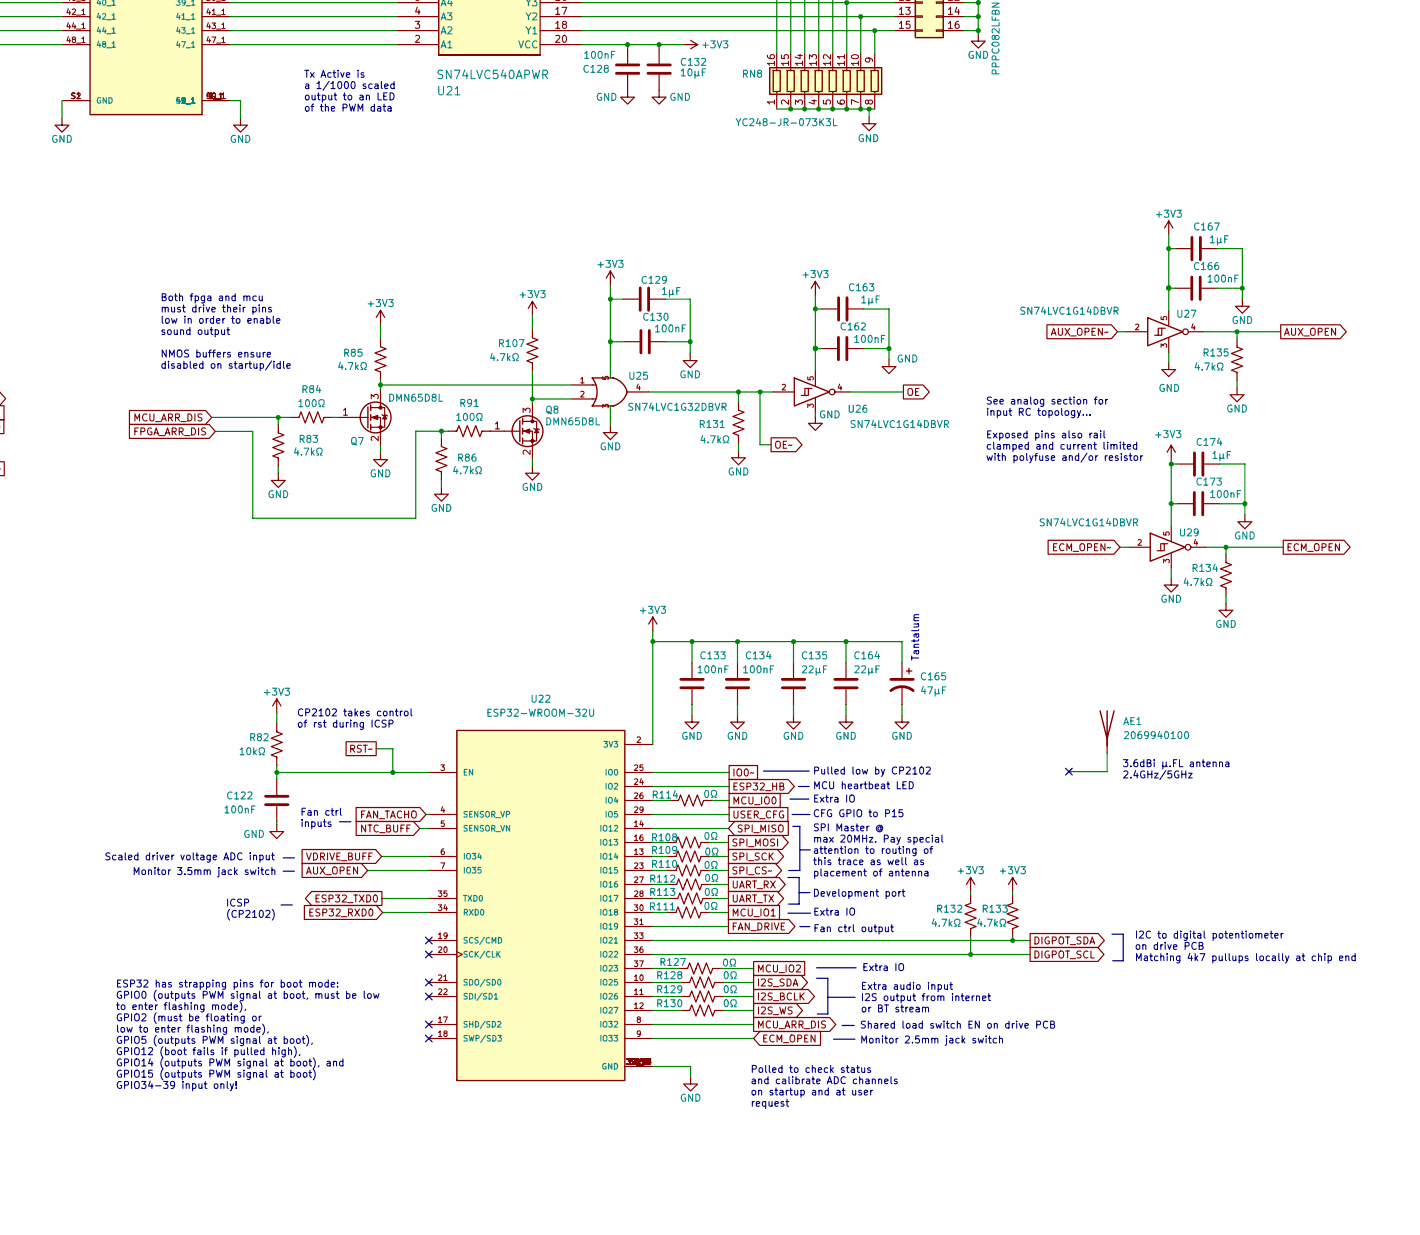
[picture p47: schematic control_Digital.kicad_sch, part in row 2, column 2]

Parts:
AE1: 2069940100
C94, C95, C98, C99, C100, C125, C126, C131, C132: 10µF; C_0603
C96, C97, C101, C102, C104, C105, C110, C113, C115, C116, C117, C118, C119, C120, C121, C122, C123, C124, C127, C128, C130, C133, C134, C162, C166, C173: 100nF; C_0603
C103, C106, C107, C108, C109, C111, C112, C114, C135, C164: 22µF; C_0603
C129, C163, C167, C174: 1µF; C_0603
C165: 47µF; C_TANT_3216-18_Kemet-A
D5, D19: BL-HB333Q-AV-TRB; D_1206
D6, D7, D8, D9, D18, D20, D21, D22: ESD7351XV2T1G; D_SOD_523
D23, D24, D25: LESD5D5.0CT1G; D_SOD_523
P1, P2, P3, P4, P5, P6, P7, P8: PPPC082LFBN-RC; PinSocket_2x08_P2.54mm_Vertical
P10, P17: B2B-PH-K-S; JST_PH_B2B-PH-K_1x02_P2.00mm_Vertical
P14: S8B-PH-K-S; JST_PH_S8B-PH-K_1x08_P2.00mm_Horizontal
P15: PH2RA-02-UA; PinHeader_2x01_P2.54mm_Horizontal
P18: S3B-PH-K-S; JST_PH_S3B-PH-K_1x03_P2.00mm_Horizontal
P21: Molex-105017; USB_Micro-B_Molex-105017-0001_Alt
PTC1: 0603L010; R_0603
PTC2, PTC3, PTC4, PTC5, PTC6, PTC7, PTC8, PTC9: 0ZCM0001FF2G; R_0603
Q1, Q2, Q3, Q4, Q7, Q8: DMN65D8L; T_SOT23
R59, R64: 1.2kΩ; R_0603
R60, R65, R68, R72, R73, R77, R78, R79, R80, R81, R108, R109, R110, R111, R112, R113, R114, R127, R128, R129, R130: 0Ω; R_0603
R61, R63, R67, R69, R70, R83, R85, R86, R107, R131, R132, R133, R134, R135: 4.7kΩ; R_0603
R62, R66, R84, R91: 100Ω; R_0603
R71: 22.1kΩ; R_0603
R74: 47.5kΩ; R_0603
R75, R76: 1kΩ; R_0603
R82: 10kΩ; R_0603
RN1, RN2, RN3, RN4, RN5, RN6, RN7, RN8: YC248-JR-073K3L; R_ARR_1606_CONVEX
SW2: B3U-1000P; SW_SPST_B3U-1000P
U12: CP2102N-A02-GQFN28; IC_QFN-28_EP_5x5
U13, U14, U15, U16, U18, U19, U20, U21: SN74LVC540APWR; IC_TSSOP-20_0.65P
U17: TE0725-03-35-2C; MODULE_TE0725-03-35-2C; PARTREV 03
U22: ESP32-WROOM-32U; MODULE_ESP32-WROOM-32D; PARTREV 1.9
U25: SN74LVC1G32DBVR; IC_SOT23-5
U26, U27, U29: SN74LVC1G14DBVR; IC_SOT23-5

Connections:
+3V3: C94.2, C95.2, C96.2, C97.2, C98.2, C99.2, C100.2, C101.2, C102.2, C103.2, C105.2, C106.2, C107.2, C108.2, C109.2, C111.2, C112.2, C113.2, C114.2, C115.2, C116.2, C117.2, C118.2, C119.2, C120.2, C121.2, C123.2, C124.2, C125.2, C126.2, C127.2, C128.2, C129.1, C130.1, C131.2, C132.2, C133.2, C134.2, C135.2, C162.1, C163.1, C164.2, C165.1, C166.1, C167.1, C173.1, C174.1, P2.2, P2.4, P15.2, PTC1.2, R59.2, R64.2, R75.1, R82.1, R85.1, R107.1, R132.2, R133.2, U12.6 (VDD), U12.7 (VREGIN), U13.20 (VCC), U14.20 (VCC), U15.20 (VCC), U16.20 (VCC), U17.1_2, U17.2_2, U17.5_1, U17.6_1, U17.45_1, U17.46_1, U17.49_2, U17.50_2, U18.20 (VCC), U19.20 (VCC), U20.20 (VCC), U21.20 (VCC), U22.2 (3V3), U25.5, U26.5, U27.5, U29.5
+VSW: P8.8
AUX_OPEN: R135.1, U22.7 (IO35), U27.4
AUX_OPEN~: U27.2
Artix7_HB: R62.1, R63.1, U17.28_1
D+: D24.2 (A2), P21.3 (D+), U12.4 (D+)
D-: D25.2 (A2), P21.2 (D-), U12.5 (D-)
DIGPOT_SCL: P8.12, R132.1, U22.36 (IO22)
DIGPOT_SDA: P8.16, R133.1, U22.33 (IO21)
DTR: Q3.2 (S), R70.1
DTR~: U12.28 (~DTR)
ECM_OPEN: R134.1, U22.9 (IO33), U29.4
ECM_OPEN~: U29.2
ESP32_HB: R66.1, R67.1, U22.24 (IO2)
ESP32_RXD0: U12.26 (TXD), U22.34 (RXD0)
ESP32_TXD0: U12.25 (RXD), U22.35 (TXD0)
FAN_DRIVE: P5.4, U22.31 (IO19)
FAN_PWM: P5.16, U17.28_2
FAN_TACHO: P5.12, U22.4 (SENSOR_VP)
FPGA_ARR_DIS: R86.1, R91.1, U17.30_2
FPGA_IO0: D8.2 (A2), PTC6.2, R79.2
FPGA_IO1: D7.2 (A2), PTC2.2, R80.2
FPGA_IO2: D6.2 (A2), PTC5.2, R81.2
GND: C94.1, C95.1, C96.1, C97.1, C98.1, C99.1, C100.1, C101.1, C102.1, C103.1, C104.1, C105.1, C106.1, C107.1, C108.1, C109.1, C110.2, C111.1, C112.1, C113.1, C114.1, C115.1, C116.1, C117.1, C118.1, C119.1, C120.1, C121.1, C122.1, C123.1, C124.1, C125.1, C126.1, C127.1, C128.1, C129.2, C130.2, C131.1, C132.1, C133.1, C134.1, C135.1, C162.2, C163.2, C164.1, C165.2, C166.2, C167.2, C173.2, C174.2, D6.1 (A1), D7.1 (A1), D8.1 (A1), D9.1 (A1), D18.1 (A1), D20.1 (A1), D21.1 (A1), D22.1 (A1), D23.1 (A1), D24.1 (A1), D25.1 (A1), P1.2, P1.4, P1.6, P1.8, P1.10, P1.12, P1.14, P1.16, P2.6, P2.8, P2.10, P2.12, P2.14, P2.16, P3.2, P3.4, P3.6, P3.8, P3.10, P3.12, P3.14, P3.16, P4.4, P4.8, P4.10, P4.12, P4.14, P4.16, P5.2, P5.6, P5.10, P5.14, P6.2, P6.4, P6.6, P6.8, P6.10, P6.12, P6.14, P6.16, P7.2, P7.4, P7.6, P7.8, P7.10, P7.12, P7.14, P7.16, P8.2, P8.4, P8.6, P8.10, P8.14, P14.8, P18.2, P21.5 (GND), Q1.2 (S), Q2.2 (S), Q7.2 (S), Q8.2 (S), R61.2, R63.2, R67.2, R68.1, R72.2, R73.1, R74.2, R76.2, R83.2, R86.2, R131.2, R134.2, R135.2, RN1.1 (R1.1), RN1.2 (R2.1), RN1.3 (R3.1), RN1.4 (R4.1), RN1.5 (R5.1), RN1.6 (R6.1), RN1.7 (R7.1), RN1.8 (R8.1), RN2.1 (R1.1), RN2.2 (R2.1), RN2.3 (R3.1), RN2.4 (R4.1), RN2.5 (R5.1), RN2.6 (R6.1), RN2.7 (R7.1), RN2.8 (R8.1), RN3.1 (R1.1), RN3.2 (R2.1), RN3.3 (R3.1), RN3.4 (R4.1), RN3.5 (R5.1), RN3.6 (R6.1), RN3.7 (R7.1), RN3.8 (R8.1), RN4.1 (R1.1), RN4.2 (R2.1), RN4.3 (R3.1), RN4.4 (R4.1), RN4.5 (R5.1), RN4.6 (R6.1), RN4.7 (R7.1), RN4.8 (R8.1), RN5.1 (R1.1), RN5.2 (R2.1), RN5.3 (R3.1), RN5.4 (R4.1), RN5.5 (R5.1), RN5.6 (R6.1), RN5.7 (R7.1), RN5.8 (R8.1), RN6.1 (R1.1), RN6.2 (R2.1), RN6.3 (R3.1), RN6.4 (R4.1), RN6.5 (R5.1), RN6.6 (R6.1), RN6.7 (R7.1), RN6.8 (R8.1), RN7.1 (R1.1), RN7.2 (R2.1), RN7.3 (R3.1), RN7.4 (R4.1), RN7.5 (R5.1), RN7.6 (R6.1), RN7.7 (R7.1), RN7.8 (R8.1), RN8.1 (R1.1), RN8.2 (R2.1), RN8.3 (R3.1), RN8.4 (R4.1), RN8.5 (R5.1), RN8.6 (R6.1), RN8.7 (R7.1), RN8.8 (R8.1), SW2.2, U12.3 (GND), U12.29 (GND), U13.10 (GND), U13.19 (*OE2), U14.10 (GND), U14.19 (*OE2), U15.10 (GND), U15.19 (*OE2), U16.10 (GND), U16.19 (*OE2), U17.1_1, U17.2_1, U17.3_2, U17.4_2, U17.45_2, U17.46_2, U17.49_1, U17.50_1, U17.S1 (GND), U17.S2 (GND), U18.10 (GND), U18.19 (*OE2), U19.10 (GND), U19.19 (*OE2), U20.10 (GND), U20.19 (*OE2), U21.10 (GND), U21.19 (*OE2), U22.1 (GND), U22.15 (GND), U22.38 (GND), U22.39_1 (GND), U22.39_2 (GND), U22.39_3 (GND), U22.39_4 (GND), U22.39_5 (GND), U22.39_6 (GND), U22.39_7 (GND), U22.39_8 (GND), U22.39_9 (GND), U22.39_10 (GND), U22.39_11 (GND), U22.39_12 (GND), U22.39_13 (GND), U22.39_14 (GND), U22.39_15 (GND), U22.39_16 (GND), U22.39_17 (GND), U22.39_18 (GND), U22.39_19 (GND), U22.39_20 (GND), U22.39_21 (GND), U25.3, U26.3, U27.3, U29.3
I2S_BCLK: R129.2, U17.24_1
I2S_SDA: R77.1, R128.2
I2S_WS: R130.2, U17.22_1
IO0~: C110.1, Q3.3 (D), R72.1, U22.25 (IO0)
MCU_ARR_DIS: R83.1, R84.1, U22.8 (IO32)
MCU_IO0: D9.2 (A2), PTC3.2, R114.2
MCU_IO1: D18.2 (A2), PTC7.2, R111.2
MCU_IO2: D20.2 (A2), PTC4.2, R127.2
NTC: P5.8
NTC_BUFF: U22.5 (SENSOR_VN)
unnamed: D5.1 (K), P10.2, Q1.3 (D)
unnamed: D5.2 (A), P10.1, R60.2
unnamed: D19.1 (K), P17.2, Q2.3 (D)
unnamed: D19.2 (A), P17.1, R65.2
unnamed: P1.1, RN4.9 (R8.2), U14.11 (Y8)
unnamed: P1.3, RN4.10 (R7.2), U14.12 (Y7)
unnamed: P1.5, RN4.11 (R6.2), U14.13 (Y6)
unnamed: P1.7, RN4.12 (R5.2), U14.14 (Y5)
unnamed: P1.9, RN4.13 (R4.2), U14.15 (Y4)
unnamed: P1.11, RN4.14 (R3.2), U14.16 (Y3)
unnamed: P1.13, RN4.15 (R2.2), U14.17 (Y2)
unnamed: P1.15, RN4.16 (R1.2), U14.18 (Y1)
unnamed: P2.1, RN6.16 (R1.2), U19.11 (Y8)
unnamed: P2.3, RN6.15 (R2.2), U19.12 (Y7)
unnamed: P2.5, RN6.14 (R3.2), U19.13 (Y6)
unnamed: P2.7, RN6.13 (R4.2), U19.14 (Y5)
unnamed: P2.9, RN6.12 (R5.2), U19.15 (Y4)
unnamed: P2.11, RN6.11 (R6.2), U19.16 (Y3)
unnamed: P2.13, RN6.10 (R7.2), U19.17 (Y2)
unnamed: P2.15, RN6.9 (R8.2), U19.18 (Y1)
unnamed: P3.1, RN2.9 (R8.2), U16.11 (Y8)
unnamed: P3.3, RN2.10 (R7.2), U16.12 (Y7)
unnamed: P3.5, RN2.11 (R6.2), U16.13 (Y6)
unnamed: P3.7, RN2.12 (R5.2), U16.14 (Y5)
unnamed: P3.9, RN2.13 (R4.2), U16.15 (Y4)
unnamed: P3.11, RN2.14 (R3.2), U16.16 (Y3)
unnamed: P3.13, RN2.15 (R2.2), U16.17 (Y2)
unnamed: P3.15, RN2.16 (R1.2), U16.18 (Y1)
unnamed: P4.1, RN8.16 (R1.2), U21.11 (Y8)
unnamed: P4.3, RN8.15 (R2.2), U21.12 (Y7)
unnamed: P4.5, RN8.14 (R3.2), U21.13 (Y6)
unnamed: P4.7, RN8.13 (R4.2), U21.14 (Y5)
unnamed: P4.9, RN8.12 (R5.2), U21.15 (Y4)
unnamed: P4.11, RN8.11 (R6.2), U21.16 (Y3)
unnamed: P4.13, RN8.10 (R7.2), U21.17 (Y2)
unnamed: P4.15, RN8.9 (R8.2), U21.18 (Y1)
unnamed: P5.1, RN3.9 (R8.2), U13.11 (Y8)
unnamed: P5.3, RN3.10 (R7.2), U13.12 (Y7)
unnamed: P5.5, RN3.11 (R6.2), U13.13 (Y6)
unnamed: P5.7, RN3.12 (R5.2), U13.14 (Y5)
unnamed: P5.9, RN3.13 (R4.2), U13.15 (Y4)
unnamed: P5.11, RN3.14 (R3.2), U13.16 (Y3)
unnamed: P5.13, RN3.15 (R2.2), U13.17 (Y2)
unnamed: P5.15, RN3.16 (R1.2), U13.18 (Y1)
unnamed: P6.1, RN5.16 (R1.2), U18.11 (Y8)
unnamed: P6.3, RN5.15 (R2.2), U18.12 (Y7)
unnamed: P6.5, RN5.14 (R3.2), U18.13 (Y6)
unnamed: P6.7, RN5.13 (R4.2), U18.14 (Y5)
unnamed: P6.9, RN5.12 (R5.2), U18.15 (Y4)
unnamed: P6.11, RN5.11 (R6.2), U18.16 (Y3)
unnamed: P6.13, RN5.10 (R7.2), U18.17 (Y2)
unnamed: P6.15, RN5.9 (R8.2), U18.18 (Y1)
unnamed: P7.1, RN1.9 (R8.2), U15.11 (Y8)
unnamed: P7.3, RN1.10 (R7.2), U15.12 (Y7)
unnamed: P7.5, RN1.11 (R6.2), U15.13 (Y6)
unnamed: P7.7, RN1.12 (R5.2), U15.14 (Y5)
unnamed: P7.9, RN1.13 (R4.2), U15.15 (Y4)
unnamed: P7.11, RN1.14 (R3.2), U15.16 (Y3)
unnamed: P7.13, RN1.15 (R2.2), U15.17 (Y2)
unnamed: P7.15, RN1.16 (R1.2), U15.18 (Y1)
unnamed: P8.1, RN7.16 (R1.2), U20.11 (Y8)
unnamed: P8.3, RN7.15 (R2.2), U20.12 (Y7)
unnamed: P8.5, RN7.14 (R3.2), U20.13 (Y6)
unnamed: P8.7, RN7.13 (R4.2), U20.14 (Y5)
unnamed: P8.9, RN7.12 (R5.2), U20.15 (Y4)
unnamed: P8.11, RN7.11 (R6.2), U20.16 (Y3)
unnamed: P8.13, RN7.10 (R7.2), U20.17 (Y2)
unnamed: P8.15, RN7.9 (R8.2), U20.18 (Y1)
unnamed: P14.1, PTC1.1
unnamed: P14.2, PTC4.1
unnamed: P14.3, PTC7.1
unnamed: P14.4, PTC3.1
unnamed: P14.5, PTC6.1
unnamed: P14.6, PTC2.1
unnamed: P14.7, PTC5.1
unnamed: P18.1, PTC9.1
unnamed: P18.3, PTC8.1
unnamed: P21.6 (Shield), R68.2
unnamed: Q1.1 (G), R62.2
unnamed: Q2.1 (G), R66.2
unnamed: Q3.1 (G), R69.2
unnamed: Q4.1 (G), R70.2
unnamed: Q7.1 (G), R84.2
unnamed: Q7.3 (D), R85.2, U25.1
unnamed: Q8.1 (G), R91.2
unnamed: Q8.3 (D), R107.2, U25.2
unnamed: R59.1, R60.1
unnamed: R64.1, R65.1
unnamed: R71.1, R74.1, U12.8 (VBUS)
unnamed: R75.2, U12.9 (~RST)
unnamed: R76.1, U12.11 (~SUSPEND)
unnamed: R77.2, U17.26_1
unnamed: R78.1, U17.23_1
unnamed: R79.1, U17.26_2
unnamed: R80.1, U17.24_2
unnamed: R81.1, U17.22_2
unnamed: R108.1, U22.16 (IO13)
unnamed: R109.1, U22.13 (IO14)
unnamed: R110.1, U22.23 (IO15)
unnamed: R111.1, U22.30 (IO18)
unnamed: R112.1, U22.27 (IO16)
unnamed: R113.1, U22.28 (IO17)
unnamed: R114.1, U22.26 (IO4)
unnamed: R127.1, U22.37 (IO23)
unnamed: R128.1, U22.10 (IO25)
unnamed: R129.1, U22.11 (IO26)
unnamed: R130.1, U22.12 (IO27)
unnamed: U13.2 (A1), U17.47_2
unnamed: U13.3 (A2), U17.43_2
unnamed: U13.4 (A3), U17.41_2
unnamed: U13.5 (A4), U17.39_2
unnamed: U13.6 (A5), U17.37_2
unnamed: U13.7 (A6), U17.35_2
unnamed: U13.8 (A7), U17.33_2
unnamed: U13.9 (A8), U17.31_2
unnamed: U14.2 (A1), U17.19_2
unnamed: U14.3 (A2), U17.17_2
unnamed: U14.4 (A3), U17.15_2
unnamed: U14.5 (A4), U17.13_2
unnamed: U14.6 (A5), U17.11_2
unnamed: U14.7 (A6), U17.9_2
unnamed: U14.8 (A7), U17.7_2
unnamed: U14.9 (A8), U17.5_2
unnamed: U15.2 (A1), U17.4_1
unnamed: U15.3 (A2), U17.8_1
unnamed: U15.4 (A3), U17.10_1
unnamed: U15.5 (A4), U17.12_1
unnamed: U15.6 (A5), U17.14_1
unnamed: U15.7 (A6), U17.16_1
unnamed: U15.8 (A7), U17.18_1
unnamed: U15.9 (A8), U17.20_1
unnamed: U16.2 (A1), U17.32_1
unnamed: U16.3 (A2), U17.34_1
unnamed: U16.4 (A3), U17.36_1
unnamed: U16.5 (A4), U17.38_1
unnamed: U16.6 (A5), U17.40_1
unnamed: U16.7 (A6), U17.42_1
unnamed: U16.8 (A7), U17.44_1
unnamed: U16.9 (A8), U17.48_1
unnamed: U17.3_1, U20.9 (A8)
unnamed: U17.6_2, U19.2 (A1)
unnamed: U17.7_1, U20.8 (A7)
unnamed: U17.8_2, U19.3 (A2)
unnamed: U17.9_1, U20.7 (A6)
unnamed: U17.10_2, U19.4 (A3)
unnamed: U17.11_1, U20.6 (A5)
unnamed: U17.12_2, U19.5 (A4)
unnamed: U17.13_1, U20.5 (A4)
unnamed: U17.14_2, U19.6 (A5)
unnamed: U17.15_1, U20.4 (A3)
unnamed: U17.16_2, U19.7 (A6)
unnamed: U17.17_1, U20.3 (A2)
unnamed: U17.18_2, U19.8 (A7)
unnamed: U17.19_1, U20.2 (A1)
unnamed: U17.20_2, U19.9 (A8)
unnamed: U17.31_1, U21.9 (A8)
unnamed: U17.32_2, U18.2 (A1)
unnamed: U17.33_1, U21.8 (A7)
unnamed: U17.34_2, U18.3 (A2)
unnamed: U17.35_1, U21.7 (A6)
unnamed: U17.36_2, U18.4 (A3)
unnamed: U17.37_1, U21.6 (A5)
unnamed: U17.38_2, U18.5 (A4)
unnamed: U17.39_1, U21.5 (A4)
unnamed: U17.40_2, U18.6 (A5)
unnamed: U17.41_1, U21.4 (A3)
unnamed: U17.42_2, U18.7 (A6)
unnamed: U17.43_1, U21.3 (A2)
unnamed: U17.44_2, U18.8 (A7)
unnamed: U17.47_1, U21.2 (A1)
unnamed: U17.48_2, U18.9 (A8)
OE: P4.6, U26.4
OE~: R131.1, U13.1 (*OE1), U14.1 (*OE1), U15.1 (*OE1), U16.1 (*OE1), U18.1 (*OE1), U19.1 (*OE1), U20.1 (*OE1), U21.1 (*OE1), U25.4, U26.2
RST: U17.30_1
RST~: C104.2, C122.2, Q4.3 (D), R73.2, R82.2, SW2.1, U22.3 (EN)
RTS: Q4.2 (S), R69.1
RTS~: U12.24 (~RTS)
SPI_CS~: R110.2, U17.27_1
SPI_MISO: R78.2, U22.14 (IO12)
SPI_MOSI: R108.2, U17.25_1
SPI_SCK: R109.2, U17.21_1
TX_ACTIVE: P4.2, U17.29_1
UART_RX: D22.2 (A2), PTC8.2, R112.2
UART_TX: D21.2 (A2), PTC9.2, R113.2
USER_CFG: P15.1, R61.1, U22.29 (IO5)
VBUS: D23.2 (A2), P21.1 (VBUS), R71.2
VDRIVE_BUFF: U22.6 (IO34)
adc_CS~: U17.21_2
adc_SCK: U17.29_2
adc_SDI: U17.27_2
adc_SDOA: U17.23_2
adc_SDOB/~ALRT: U17.25_2

Notes on the sheet:
Extra audio input I2S output from internet or BT stream
Scaled driver voltage ADC input
Headers P1-P8 correspond 1:1 to headers P1-P8 on the ultrasonic drive board
Polled to check status and calibrate ADC channels on startup and at user request
System RST
Pulled low by CP2102
CFG GPIO to P15
Extra IO
3V3 rail on driver board
Populate jumper to configure various GPIO outputs to P15 (An I2S bus is possible, alternatively some feature TBD) This is a right angle standard pitch header next to the micro.
3.6dBi µ.FL antenna 2.4GHz/5GHz
MCU heartbeat LED
Remote board uses header with Rx, Tx flipped and a 1:1 harness
Monitor 3.5mm jack switch
100mA hold 300mA trip
CP2102 takes control of rst during ICSP
Use partsExpress PN 320-343 for 3pos shielded UART
I2C to digital potentiometer on drive PCB Matching 4k7 pullups locally at chip end
Tantalum
Development port
Fan ctrl inputs
Desired height from board ~ 10mm 2.5mm spacer common to pinheaders 7.5mm female receptacle for 6mm long pins then use 10mm standoffs for mounting Add 0.5mm - 1mm washers to increase height of mounting posts for better fit.
Blue 2.8V typ. at 5mA (3.2V max) 15mcd lumunious intensity at 5mA, 120deg viewing angle
Controller PCB - DIGITAL
Both fpga and mcu must drive their pins low in order to enable sound output NMOS buffers ensure disabled on startup/idle
See analog section for input RC topology... Exposed pins also rail clamped and current limited with polyfuse and/or resistor
Shared load switch EN on drive PCB
Use AdaFruit PN 4714 and PN 3814 mating harnesses for panel mount LED solution. 3x needed for this board.
15Ω nom. 10mA hold 30mA trip
Monitor 2.5mm jack switch
ICSP (CP2102)
ESP32 has strapping pins for boot mode: GPIO0 (outputs PWM signal at boot, must be low to enter flashing mode), GPIO2 (must be floating or low to enter flashing mode), GPIO5 (outputs PWM signal at boot), GPIO12 (boot fails if pulled high), GPIO14 (outputs PWM signal at boot), and GPIO15 (outputs PW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
Fan ctrl output
Extra GPIO output 3x MCU, 3x FPGA GPIO, 3V3, and GND
Tx Active is a 1/1000 scaled output to an LED of the PWM data
SPI Master @ max 20MHz. Pay special attention to routing of this trace as well as placement of antenna
Micro-B USB programming header for ESP32
