kharper55/soundSteering_CAD_FINAL/Ultrasonic Sound Steering - Control Rev. B/otherStuff/control_Power.kicad_sch

## KiCad design Ultrasonic Sound Steering - Control Rev. B/otherStuff/control_Power.kicad_sch (2024-05-02)

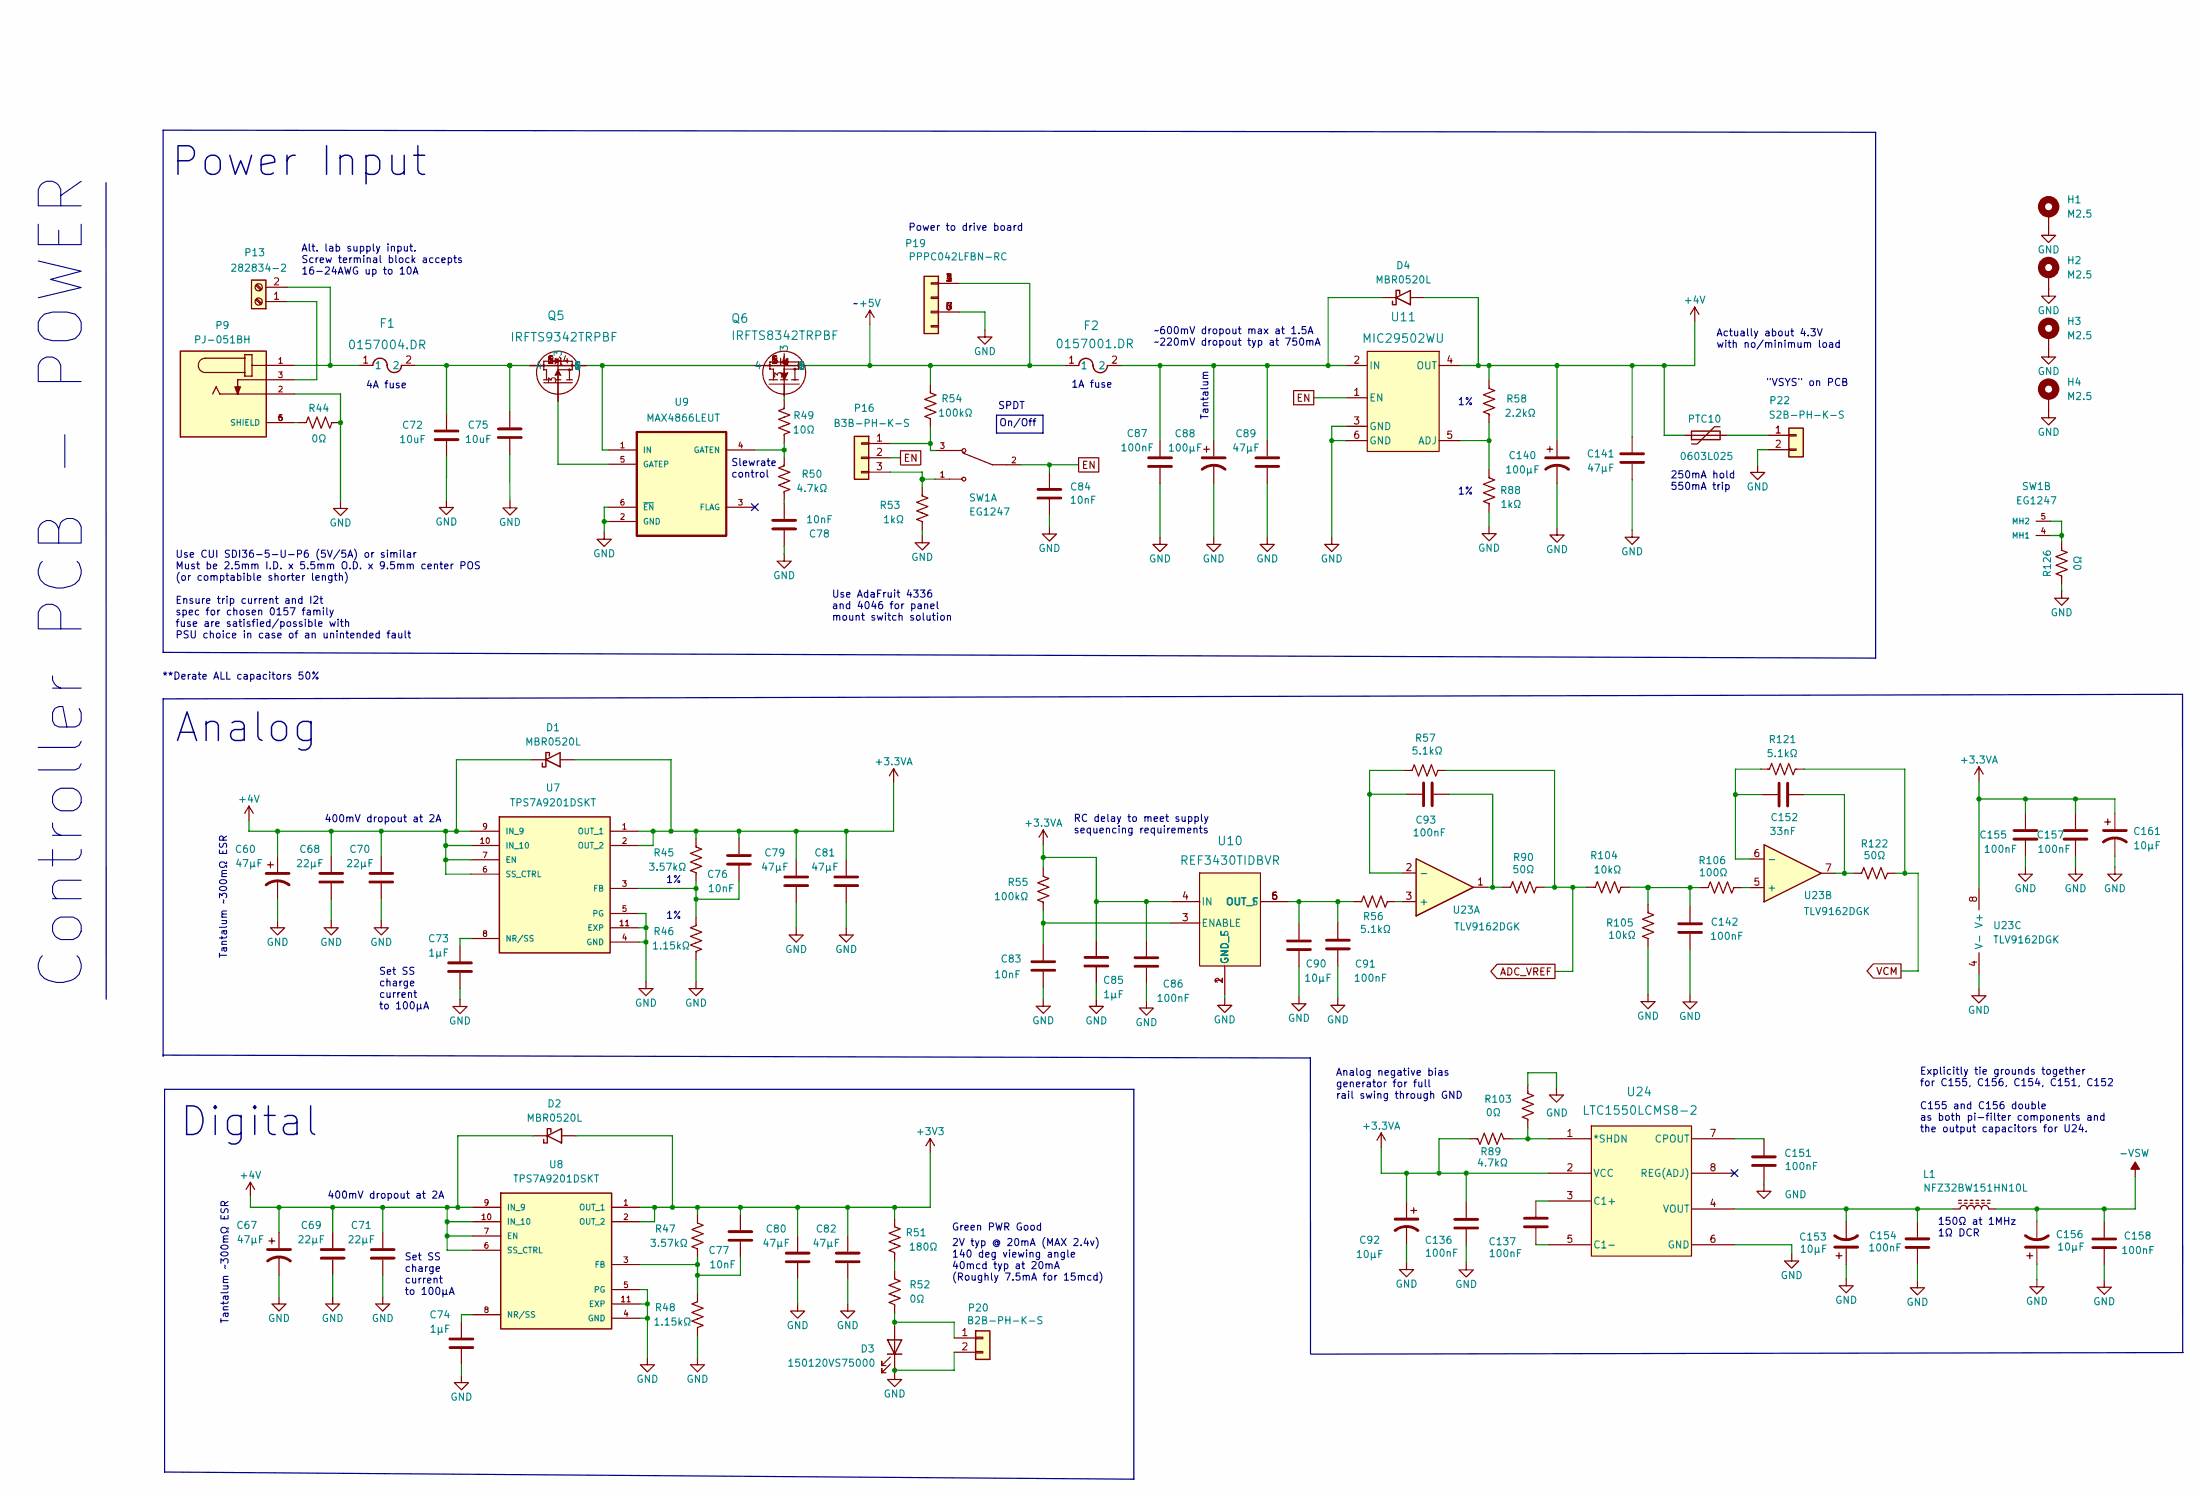
[picture p48: schematic control_Power.kicad_sch]

Parts:
C60, C67: 47µF; C_TANT_3216-18_Kemet-A
C68, C69, C70, C71: 22µF; C_0603
C72, C75: 10uF; C_0603
C73, C74, C85: 1µF; C_0603
C76, C77, C78, C83, C84: 10nF; C_0603
C79, C80, C81, C82, C89, C141: 47µF; C_0603
C86, C87, C91, C93, C136, C137, C142, C151, C154, C155, C157, C158: 100nF; C_0603
C88, C140: 100µF; C_TANT_3528-21_Kemet-B
C90: 10µF; C_0603
C92, C161: 10µF; C_TANT_3216-18_Kemet-A
C152: 33nF; C_0603
C153, C156: 10µF; C_TANT_1608-10
D1, D2, D4: MBR0520L; D_SOD_123
D3: 150120VS75000; D_1206
F1: 0157004.DR; F_0157_SMD2
F2: 0157001.DR; F_0157_SMD2
H1, H2, H3, H4: M2.5; MountingHole_2.7mm_M2.5_DIN965_Pad_TopBottom
L1: NFZ32BW151HN10L; R_0603
P9: PJ-051BH; CUI_PJ-051BH; DigiKey_Part_Number CP-051BH-ND
P13: 282834-2; TE_282834-2
P16: B3B-PH-K-S; JST_PH_B2B-PH-K_1x02_P2.00mm_Vertical
P19: PPPC042LFBN-RC; PinSocket_2x04_P2.54mm_Vertical
P20: B2B-PH-K-S; JST_PH_B2B-PH-K_1x02_P2.00mm_Vertical
P22: S2B-PH-K-S; JST_PH_B2B-PH-K_1x02_P2.00mm_Vertical
PTC10: 0603L025; R_0603
Q5: IRFTS9342TRPBF; IC_SOT23-6
Q6: IRFTS8342TRPBF; IC_SOT23-6
R44, R52, R103, R126: 0Ω; R_0603
R45, R47: 3.57kΩ; R_0603
R46, R48: 1.15kΩ; R_0603
R49: 10Ω; R_0603
R50, R89: 4.7kΩ; R_0603
R51: 180Ω; R_0603
R53, R88: 1kΩ; R_0603
R54, R55: 100kΩ; R_0603
R56, R57, R121: 5.1kΩ; R_0603
R58: 2.2kΩ; R_0603
R90, R122: 50Ω; R_0603
R104, R105: 10kΩ; R_0603
R106: 100Ω; R_0603
SW1: EG1247; SW_EG1247
U7, U8: TPS7A9201DSKT; IC_SON-10_EP_2.5X2.5; PARTREV December 2016
U9: MAX4866LEUT; IC_SOT23-6
U10: REF3430TIDBVR; IC_SOT23-6
U11: MIC29502WU; IC_TO263-5
U23: TLV9162DGK; IC_VSSOP-8_0.65P
U24: LTC1550LCMS8-2; IC_MSOP-8_3x3mm_P0.65

Connections:
+3.3VA: C76.2, C79.2, C81.2, C85.2, C86.2, C92.1, C136.1, C155.1, C157.1, C161.1, D1.2 (A), R45.2, R55.2, R89.2, U7.1 (OUT_1), U7.2 (OUT_2), U10.4 (IN), U23.8 (V+), U24.2 (VCC)
+3V3: C77.2, C80.2, C82.2, D2.2 (A), R47.2, R51.2, U8.1 (OUT_1), U8.2 (OUT_2)
+4V: C60.1, C67.1, C68.2, C69.2, C70.2, C71.2, C140.1, C141.2, D1.1 (K), D2.1 (K), D4.2 (A), PTC10.1, R58.2, U7.6 (SS_CTRL), U7.7 (EN), U7.9 (IN_9), U7.10 (IN_10), U8.6 (SS_CTRL), U8.7 (EN), U8.9 (IN_9), U8.10 (IN_10), U11.4 (OUT)
+5V: F2.1, P19.1, P19.2, P19.3, P19.4, Q6.4, R54.2
-VSW: C156.2, C158.1, L1.2
ADC_VREF: R57.2, R90.1, R104.2
EN: C84.2, P16.2, SW1.2, U11.1 (EN)
GND: C60.2, C67.2, C68.1, C69.1, C70.1, C71.1, C72.1, C73.1, C74.1, C75.1, C78.2, C79.1, C80.1, C81.1, C82.1, C83.1, C84.1, C85.1, C86.1, C87.1, C88.2, C89.1, C90.1, C91.1, C92.2, C136.2, C140.2, C141.1, C142.1, C151.2, C153.1, C154.2, C155.2, C156.1, C157.2, C158.2, C161.2, D3.1 (K), H1.1, H2.1, H3.1, H4.1, P9.2, P19.5, P19.6, P19.7, P19.8, P20.2, P22.2, R44.1, R46.1, R48.1, R53.1, R88.1, R103.1, R105.2, R126.2, U7.4 (GND), U7.5 (PG), U7.11 (EXP), U7.12, U7.13 (IN_9), U7.14 (1), U7.15 (1), U8.4 (GND), U8.5 (PG), U8.11 (EXP), U8.12, U8.13 (IN_9), U8.14 (1), U8.15 (1), U9.2 (GND), U9.6 (~EN), U10.1 (GND_F), U10.2 (GND_S), U11.3 (GND), U11.6 (GND), U23.4 (V-), U24.6 (GND)
unnamed: C72.2, C75.2, F1.2
unnamed: C73.2, U7.8 (NR/SS)
unnamed: C74.2, U8.8 (NR/SS)
unnamed: C76.1, R45.1, R46.2, U7.3 (FB)
unnamed: C77.1, R47.1, R48.2, U8.3 (FB)
unnamed: C78.1, R50.1
unnamed: C83.2, R55.1, U10.3 (ENABLE)
unnamed: C87.2, C88.1, C89.2, D4.1 (K), F2.2, U11.2 (IN)
unnamed: C90.2, C91.2, R56.1, U10.5 (OUT_S), U10.6 (OUT_F)
unnamed: C93.1, R90.2, U23.1
unnamed: C93.2, R57.1, U23.2 (-)
unnamed: C137.1, U24.3 (C1+)
unnamed: C137.2, U24.5 (C1-)
unnamed: C142.2, R104.1, R105.1, R106.1
unnamed: C151.1, U24.7 (CPOUT)
unnamed: C152.1, R122.2, U23.7
unnamed: C152.2, R121.1, U23.6 (-)
unnamed: C153.2, C154.1, L1.1, U24.4 (VOUT)
unnamed: D3.2 (A), P20.1, R52.2
unnamed: F1.1, P9.1, P13.2
unnamed: P9.5 (SHIELD), P9.6 (SHIELD), R44.2
unnamed: P9.3, P13.1
unnamed: P16.1, R54.1, SW1.3
unnamed: P16.3, R53.2, SW1.1
unnamed: P22.1, PTC10.2
unnamed: Q5.1, Q5.2, Q5.5, Q5.6
unnamed: Q5.3, U9.5 (GATEP)
unnamed: Q5.4, Q6.1, Q6.2, Q6.5, Q6.6, U9.1 (IN)
unnamed: Q6.3, R49.2
unnamed: R49.1, R50.2, U9.4 (GATEN)
unnamed: R51.1, R52.1
unnamed: R56.2, U23.3 (+)
unnamed: R58.1, R88.2, U11.5 (ADJ)
unnamed: R89.1, R103.2, U24.1 (*SHDN)
unnamed: R106.2, U23.5 (+)
unnamed: R126.1, SW1.4 (MH1), SW1.5 (MH2)
VCM: R121.2, R122.1

Notes on the sheet:
Slewrate control
Actually about 4.3V with no/minimum load
4A fuse
Tantalum ~300mΩ ESR
Set SS charge current to 100µA
Analog
Controller PCB - POWER
~600mV dropout max at 1.5A ~220mV dropout typ at 750mA
PWR Good
Power Input
**Derate ALL capacitors 50%
RC delay to meet supply sequencing requirements
400mV dropout at 2A
Analog negative bias generator for full rail swing through GND
2V typ @ 20mA (MAX 2.4v) 140 deg viewing angle 40mcd typ at 20mA (Roughly 7.5mA for 15mcd)
Green
Use CUI SDI36-5-U-P6 (5V/5A) or similar Must be 2.5mm I.D. x 5.5mm O.D. x 9.5mm center POS (or comptabible shorter length) Ensure trip current and I2t spec for chosen 0157 family fuse are satisfied/possible with PSU choice in case of an unintended fault
250mA hold 550mA trip
150Ω at 1MHz 1Ω DCR
Tantalum
Alt. lab supply input. Screw terminal block accepts 16-24AWG up to 10A
Use AdaFruit 4336 and 4046 for panel mount switch solution
Power to drive board
Digital
"VSYS" on PCB
On/Off
1A fuse
Explicitly tie grounds together for C155, C156, C154, C151, C152 C155 and C156 double as both pi-filter components and the output capacitors for U24.
SPDT
