kharper55/soundSteering_CAD_FINAL/Ultrasonic Sound Steering - Driver Rev. C/otherStuff/drive_Power.kicad_sch

## KiCad design Ultrasonic Sound Steering - Driver Rev. C/otherStuff/drive_Power.kicad_sch (2024-05-02)

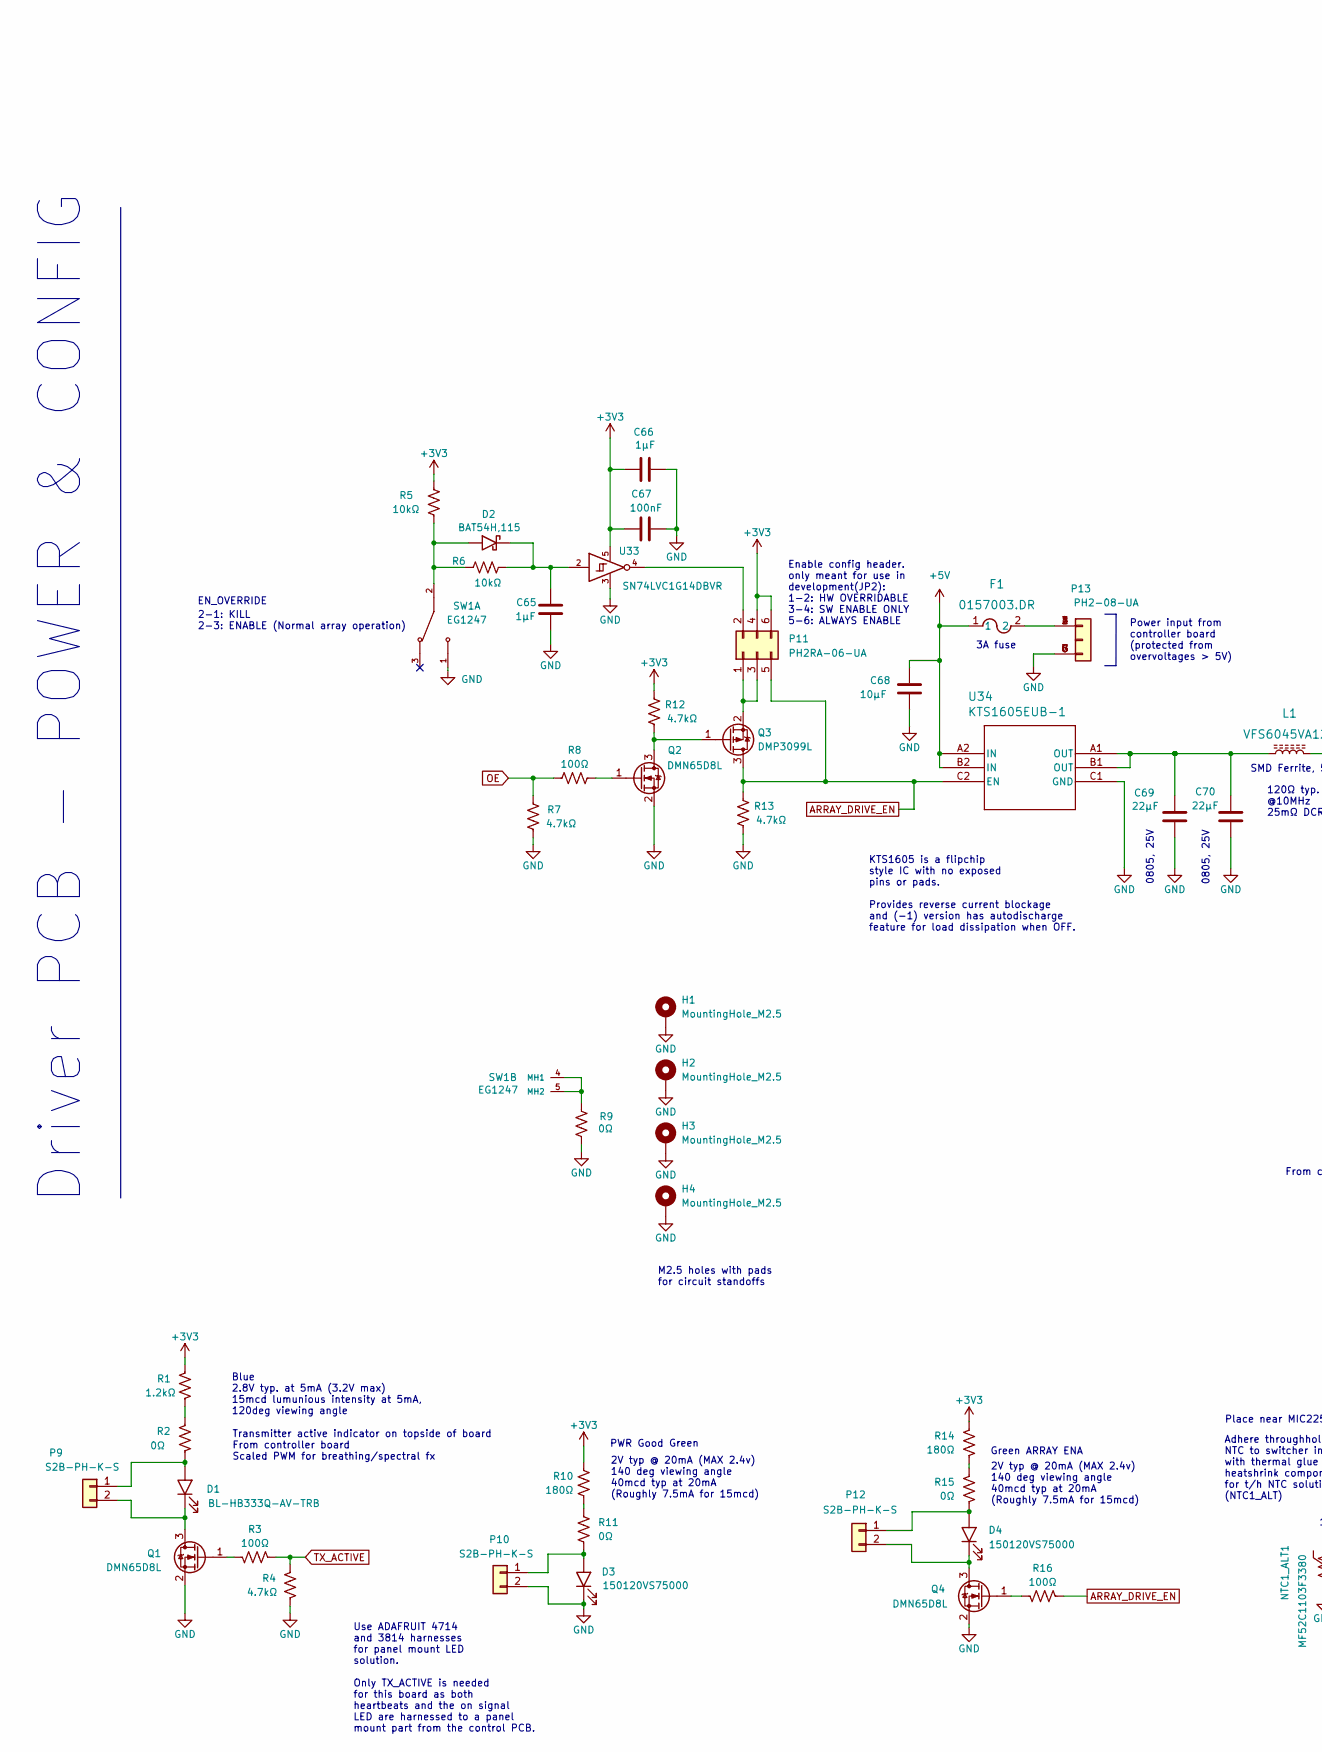
[picture p49: schematic drive_Power.kicad_sch, part in row 1, column 1]

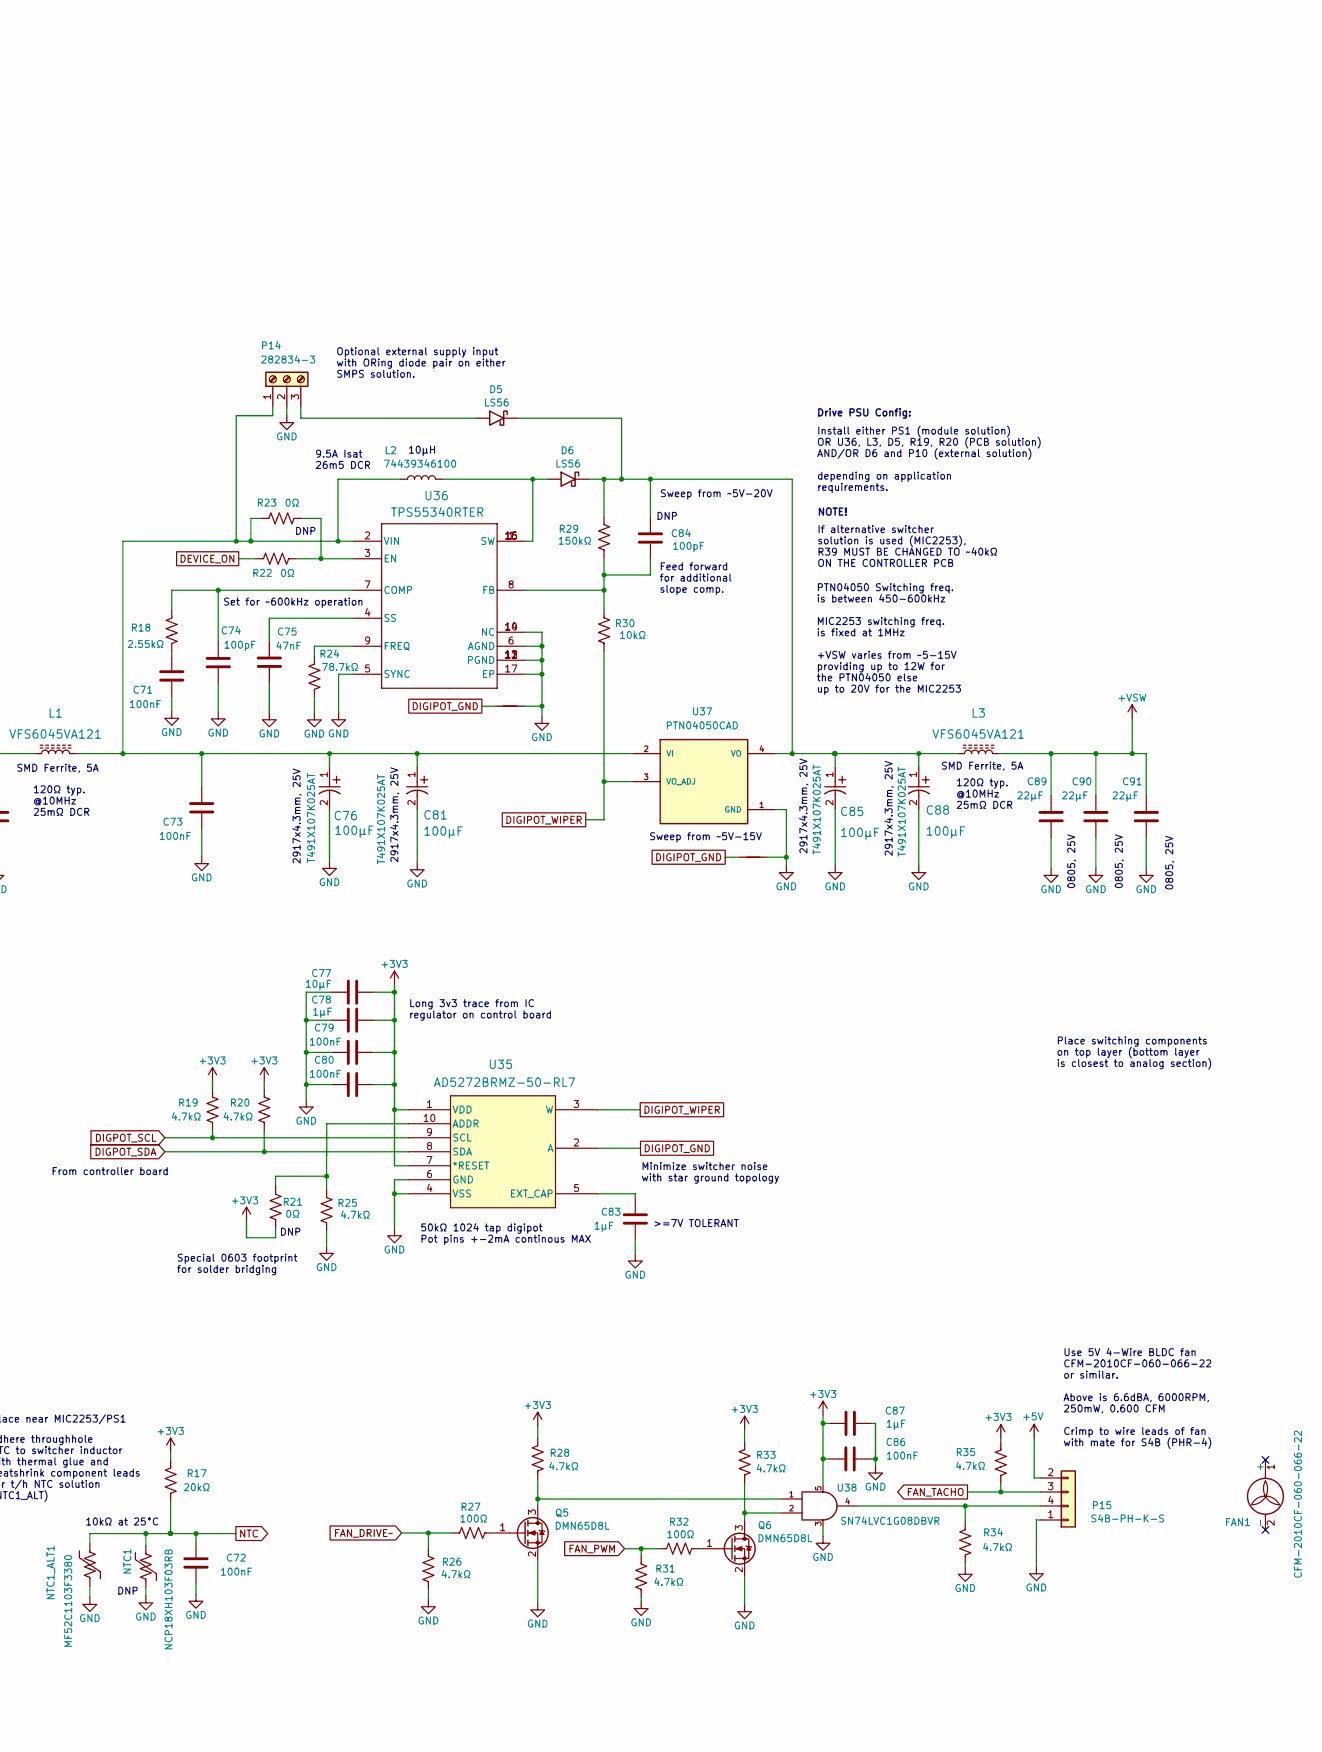
[picture p50: schematic drive_Power.kicad_sch, part in row 1, column 2]

Parts:
C65, C66, C78, C83, C87: 1µF; C_0603
C67, C72, C79, C80, C86: 100nF; C_0603
C68: 10µF; C_0805
C69, C70, C89, C90, C91: 22µF; C_0805
C71, C73: 100nF; C_0805
C74, C84: 100pF; C_0805
C75: 47nF; C_0805
C76, C81, C85, C88: 100µF; C_TANT_7343_Kemet
C77: 10µF; C_0603
D1: BL-HB333Q-AV-TRB; D_1206
D2: BAT54H,115; D_SOD_123F
D3, D4: 150120VS75000; D_1206
D5, D6: LS56; D_DO-221AC
F1: 0157003.DR; F_0157_SMD2
FAN1: CFM-2010CF-060-066-22
H1, H2, H3, H4: MountingHole_M2.5; MountingHole_2.7mm_M2.5_DIN965_Pad
L1, L3: VFS6045VA121; L_2424_6x6_4.5H
L2: 74439346100; L_SMD2_WURTH_6.45x6.45x5.8H
NT1, NT2: NetTie_2
NTC1: NCP18XH103F03RB; R_0603
NTC1_ALT1: MF52C1103F3380; R_DIN0204
P9, P10, P12: S2B-PH-K-S; JST_PH_S2B-PH-K_1x02_P2.00mm_Horizontal
P11: PH2RA-06-UA; PinHeader_2x03_P2.54mm_Horizontal
P13: PH2-08-UA; PinHeader_2x04_P2.54mm_Vertical
P14: 282834-3; TE_282834-3
P15: S4B-PH-K-S; JST_PH_S4B-PH-K_1x04_P2.00mm_Horizontal
Q1, Q2, Q4, Q5, Q6: DMN65D8L; T_SOT23
Q3: DMP3099L; T_SOT23
R1: 1.2kΩ; R_0603
R2, R9, R11, R15, R21, R22, R23: 0Ω; R_0603
R3, R8, R16, R27, R32: 100Ω; R_0603
R4, R7, R12, R13, R19, R20, R25, R26, R28, R31, R33, R34, R35: 4.7kΩ; R_0603
R5, R6, R30: 10kΩ; R_0603
R10, R14: 180Ω; R_0603
R17: 20kΩ; R_0603
R18: 2.55kΩ; R_0603
R24: 78.7kΩ; R_0603
R29: 150kΩ; R_0603
SW1: EG1247; SW_EG1247
U33: SN74LVC1G14DBVR; IC_SOT23-5
U34: KTS1605EUB-1; IC_WLCSP-6_0.5P
U35: AD5272BRMZ-50-RL7; IC_MSOP-10_0.65P
U36: TPS55340RTER; IC_WQFN-16_EP_3x3
U37: PTN04050CAD; CONV_PTN04050CAD; PARTREV A
U38: SN74LVC1G08DBVR; IC_SOT23-5

Connections:
+3V3: C66.1, C67.1, C77.2, C78.2, C79.2, C80.2, C86.1, C87.1, P11.4, P11.6, R1.2, R5.1, R10.1, R12.2, R14.1, R17.2, R19.1, R20.1, R21.1, R28.1, R33.1, R35.1, U33.5, U35.1 (VDD), U35.7 (*RESET), U38.5
+5V: C68.2, F1.1, P15.2, U34.A2 (IN), U34.B2 (IN)
+VSW: C89.2, C90.2, C91.2, L3.2
ARRAY_DRIVE_EN: P11.5, Q3.3, R13.2, R16.1, U34.C2 (EN)
DEVICE_ON: R22.2
DIGIPOT_GND: NT1.2, NT2.2, U35.2 (A)
DIGIPOT_WIPER: R30.1, U35.3 (W), U37.3 (VO_ADJ)
DIGPOT_SCL: R19.2, U35.9 (SCL)
DIGPOT_SDA: R20.2, U35.8 (SDA)
FAN_DRIVE~: R26.2, R27.1
FAN_PWM: R31.2, R32.1
FAN_TACHO: P15.3, R35.2
GND: C65.2, C66.2, C67.2, C68.1, C69.1, C70.1, C71.1, C72.2, C73.1, C74.1, C75.1, C76.2, C77.1, C78.1, C79.1, C80.1, C81.2, C83.2, C85.2, C86.2, C87.2, C88.2, C89.1, C90.1, C91.1, D3.1 (K), H1.1, H2.1, H3.1, H4.1, NT1.1, NT2.1, NTC1.2, NTC1_ALT1.2, P10.2, P13.5, P13.6, P13.7, P13.8, P14.2, P15.1, Q1.2 (S), Q2.2 (S), Q4.2 (S), Q5.2 (S), Q6.2 (S), R4.1, R7.1, R9.1, R13.1, R24.1, R25.1, R26.1, R31.1, R34.2, SW1.1, U33.3, U34.C1 (GND), U35.4 (VSS), U35.6 (GND), U36.5 (SYNC), U36.6 (AGND), U36.10 (NC), U36.11 (PGND), U36.12 (PGND), U36.13 (PGND), U36.14 (NC), U36.17 (EP), U37.1 (GND), U38.3
NTC: C72.1, NTC1.1, NTC1_ALT1.1, R17.1
unnamed: C65.1, D2.1 (K), R6.2, U33.2
unnamed: C69.2, C70.2, L1.1, U34.A1 (OUT), U34.B1 (OUT)
unnamed: C71.2, R18.1
unnamed: C73.2, C76.1, C81.1, L1.2, L2.1, P14.1, R23.2, U36.2 (VIN), U37.2 (VI)
unnamed: C74.2, R18.2, U36.7 (COMP)
unnamed: C75.2, U36.4 (SS)
unnamed: C83.1, U35.5 (EXT_CAP)
unnamed: C84.1, R29.1, R30.2, U36.8 (FB)
unnamed: C84.2, C85.1, C88.1, D5.1 (K), D6.1 (K), L3.1, R29.2, U37.4 (VO)
unnamed: D1.1 (K), P9.2, Q1.3 (D)
unnamed: D1.2 (A), P9.1, R2.2
unnamed: D2.2 (A), R5.2, R6.1, SW1.2
unnamed: D3.2 (A), P10.1, R11.2
unnamed: D4.1 (K), P12.2, Q4.3 (D)
unnamed: D4.2 (A), P12.1, R15.2
unnamed: D5.2 (A), P14.3
unnamed: D6.2 (A), L2.2, U36.1 (SW), U36.15 (SW), U36.16 (SW)
unnamed: F1.2, P13.1, P13.2, P13.3, P13.4
unnamed: P11.1, P11.3, Q3.2
unnamed: P11.2, U33.4
unnamed: P15.4, R34.1, U38.4
unnamed: Q1.1 (G), R3.2
unnamed: Q2.1 (G), R8.2
unnamed: Q2.3 (D), Q3.1, R12.1
unnamed: Q4.1 (G), R16.2
unnamed: Q5.1 (G), R27.2
unnamed: Q5.3 (D), R28.2, U38.1
unnamed: Q6.1 (G), R32.2
unnamed: Q6.3 (D), R33.2, U38.2
unnamed: R1.1, R2.1
unnamed: R9.2, SW1.4 (MH1), SW1.5 (MH2)
unnamed: R10.2, R11.1
unnamed: R14.2, R15.1
unnamed: R21.2, R25.2, U35.10 (ADDR)
unnamed: R22.1, R23.1, U36.3 (EN)
unnamed: R24.2, U36.9 (FREQ)
OE: R7.2, R8.1
TX_ACTIVE: R3.1, R4.2

Notes on the sheet:
Enable config header. only meant for use in development(JP2): 1-2: HW OVERRIDABLE 3-4: SW ENABLE ONLY 5-6: ALWAYS ENABLE
Drive PSU Config:
Power input from controller board (protected from overvoltages > 5V)
NOTE!
ARRAY ENA
If alternative switcher solution is used (MIC2253), R39 MUST BE CHANGED TO ~40kΩ ON THE CONTROLLER PCB
3A fuse
From controller board
10µH
2917x4.3mm, 25V
Use ADAFRUIT 4714 and 3814 harnesses for panel mount LED solution. Only TX_ACTIVE is needed for this board as both heartbeats and the on signal LED are harnessed to a panel mount part from the control PCB.
0805, 25V
Driver PCB - POWER & CONFIG
120Ω typ. @10MHz 25mΩ DCR
Optional external supply input with ORing diode pair on either SMPS solution.
Sweep from ~5V-15V
Blue 2.8V typ. at 5mA (3.2V max) 15mcd lumunious intensity at 5mA, 120deg viewing angle
M2.5 holes with pads for circuit standoffs
Install either PS1 (module solution) OR U36, L3, D5, R19, R20 (PCB solution) AND/OR D6 and P10 (external solution) depending on application requirements.
9.5A Isat 26m5 DCR
2V typ @ 20mA (MAX 2.4v) 140 deg viewing angle 40mcd typ at 20mA (Roughly 7.5mA for 15mcd)
2-1: KILL 2-3: ENABLE (Normal array operation)
DNP
Feed forward for additional slope comp.
10kΩ at 25°C
Sweep from ~5V-20V
Long 3v3 trace from IC regulator on control board
Adhere throughhole NTC to switcher inductor with thermal glue and heatshrink component leads for t/h NTC solution (NTC1_ALT)
Green
EN_OVERRIDE
SMD Ferrite, 5A
PWR Good
Minimize switcher noise with star ground topology
PTN04050 Switching freq. is between 450-600kHz MIC2253 switching freq. is fixed at 1MHz +VSW varies from ~5-15V providing up to 12W for the PTN04050 else up to 20V for the MIC2253
Use 5V 4-Wire BLDC fan CFM-2010CF-060-066-22 or similar. Above is 6.6dBA, 6000RPM, 250mW, 0.600 CFM Crimp to wire leads of fan with mate for S4B (PHR-4)
Place near MIC2253/PS1
50kΩ 1024 tap digipot Pot pins +-2mA continous MAX
>=7V TOLERANT
KTS1605 is a flipchip style IC with no exposed pins or pads. Provides reverse current blockage and (-1) version has autodischarge feature for load dissipation when OFF.
Special 0603 footprint for solder bridging
Set for ~600kHz operation
Place switching components on top layer (bottom layer is closest to analog section)
Transmitter active indicator on topside of board From controller board Scaled PWM for breathing/spectral fx
