kharper55/soundSteering_CAD_FINAL/Ultrasonic Sound Steering - Driver Rev. C/otherStuff/drive_Transducers.kicad_sch

## KiCad design Ultrasonic Sound Steering - Driver Rev. C/otherStuff/drive_Transducers.kicad_sch (2024-05-02)

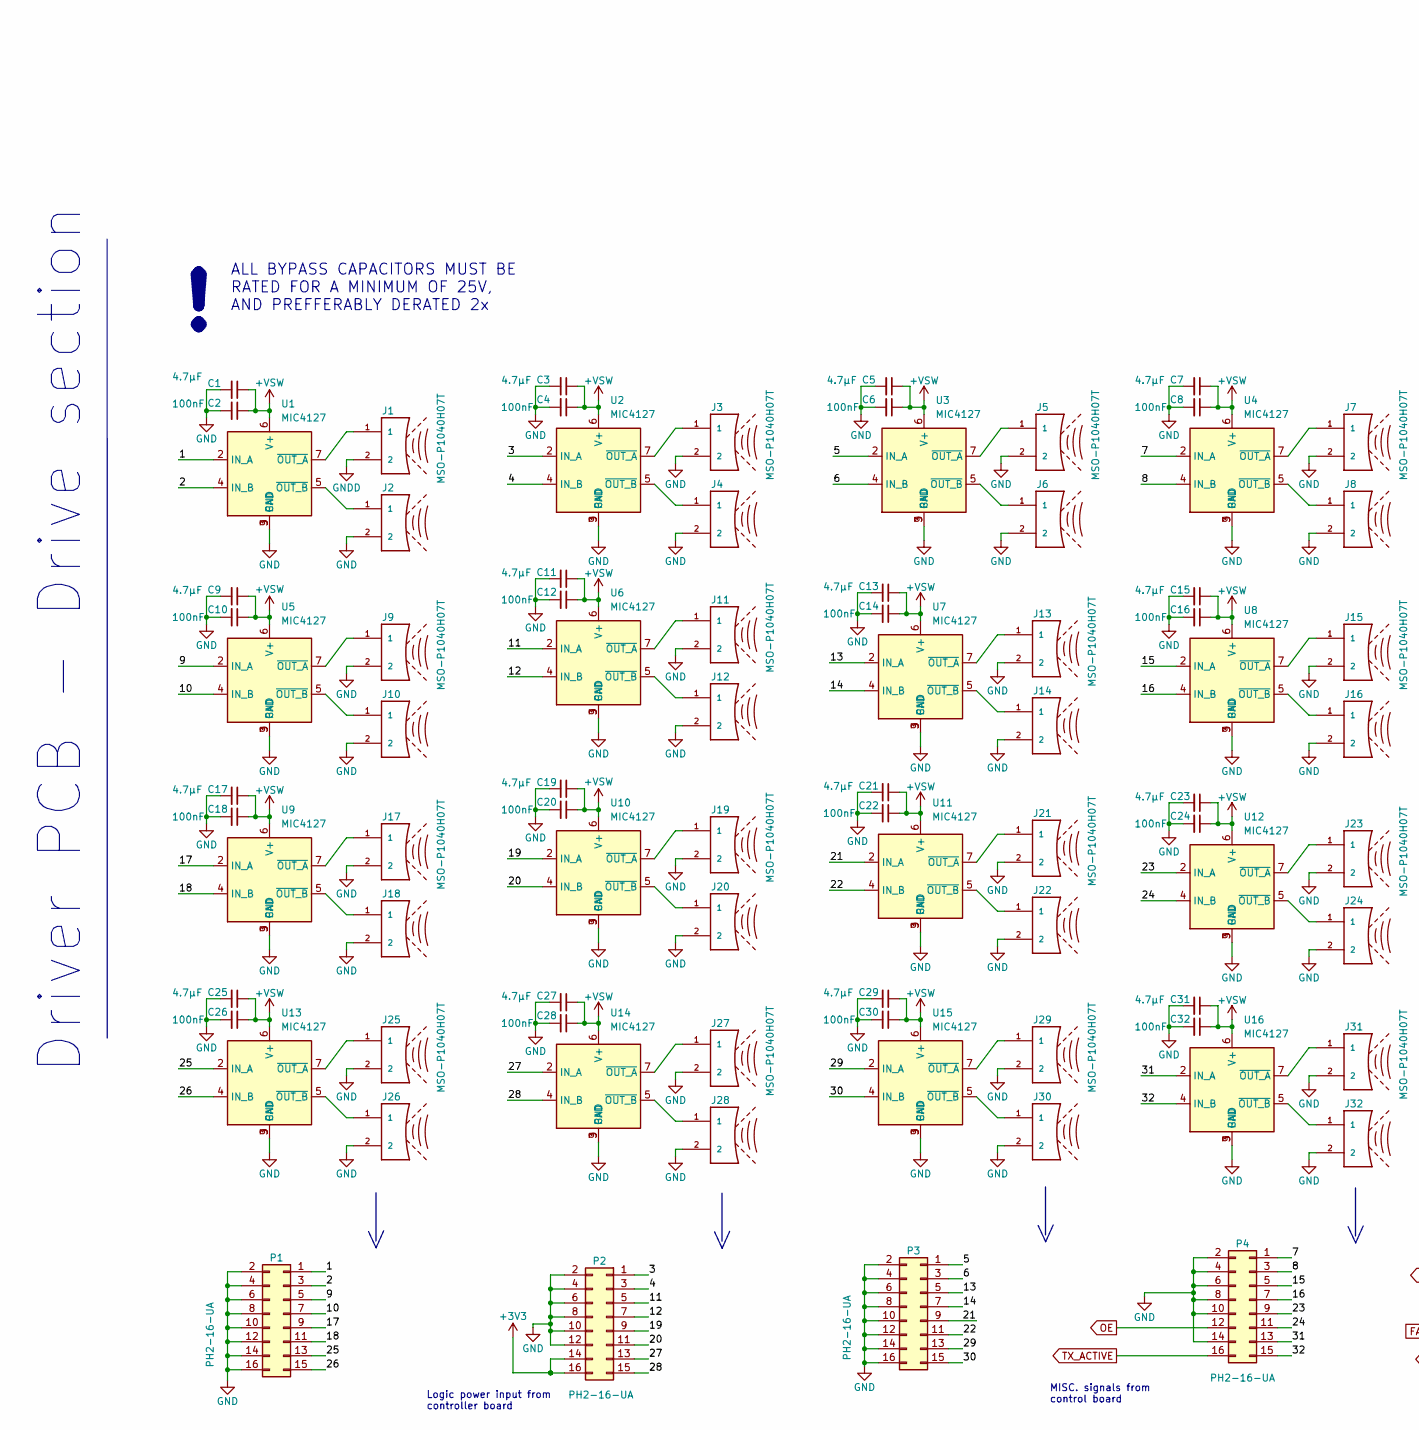
[picture p51: schematic drive_Transducers.kicad_sch, part in row 1, column 1]

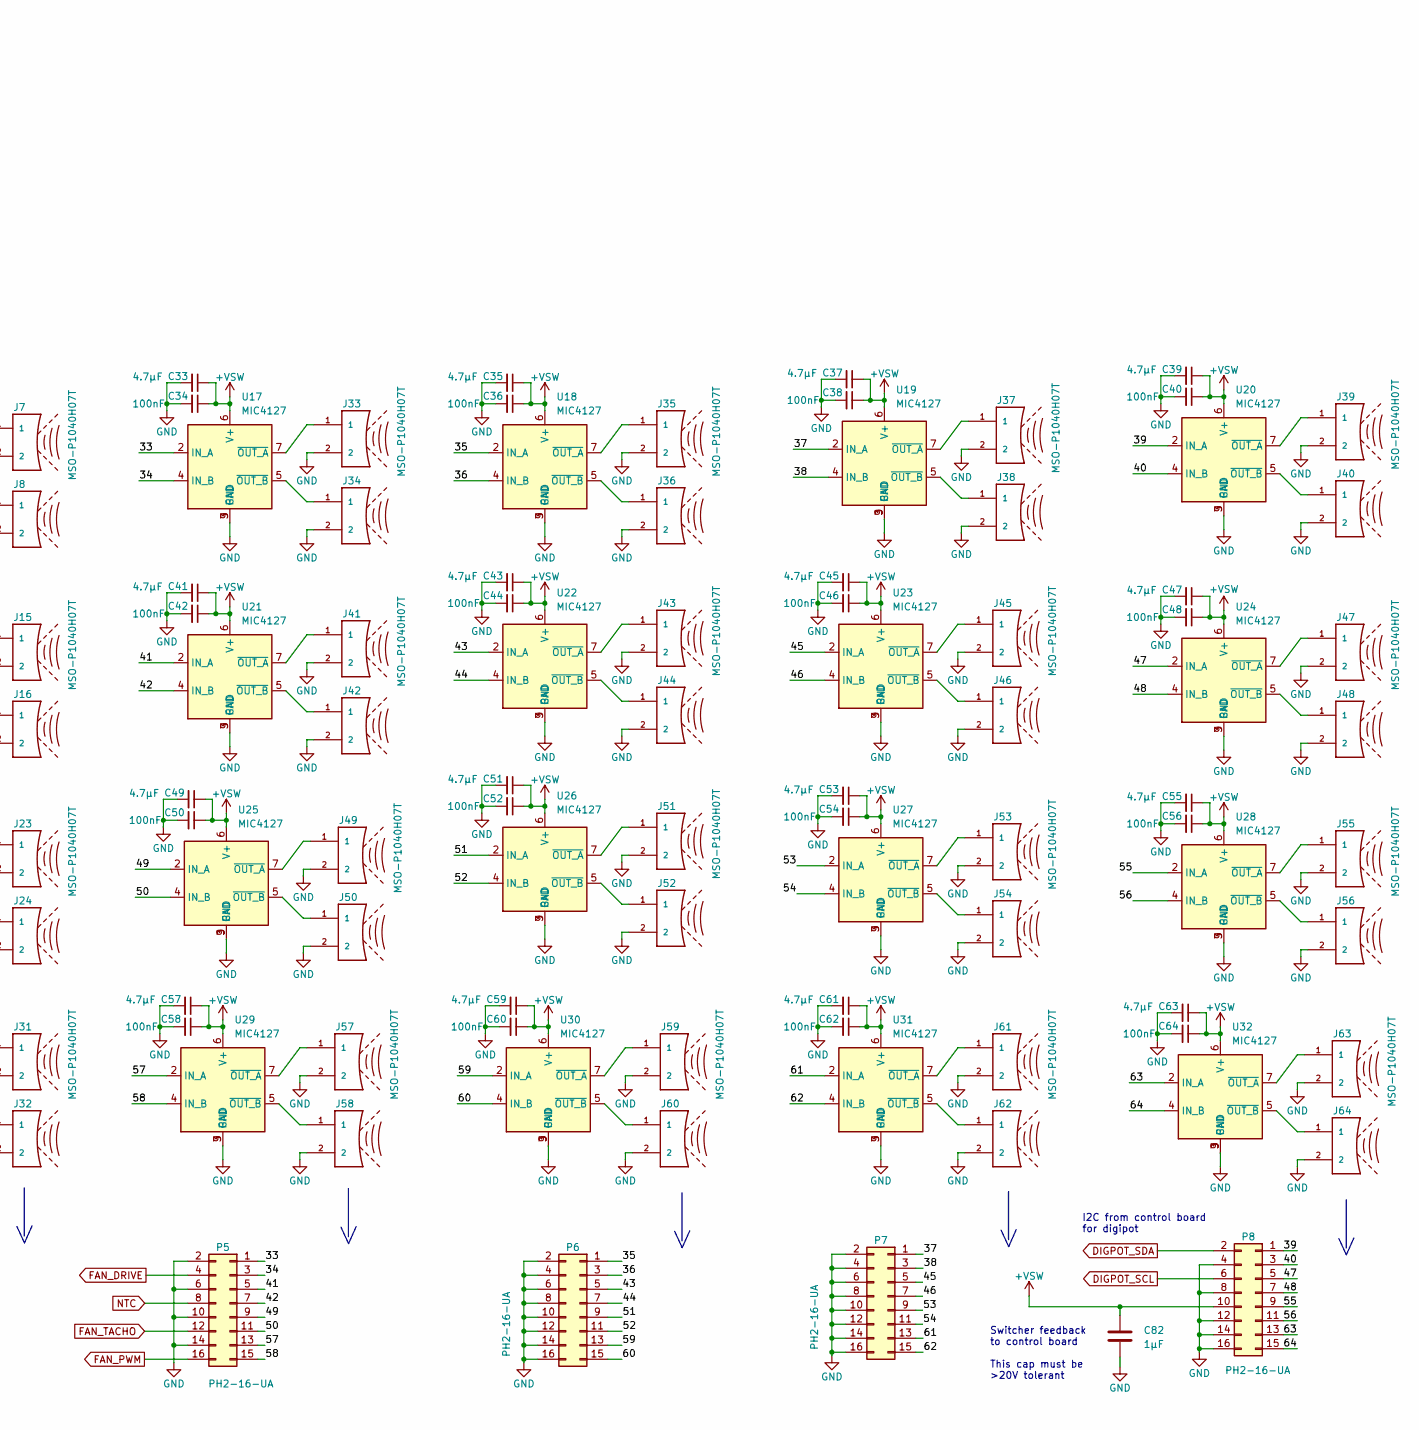
[picture p52: schematic drive_Transducers.kicad_sch, part in row 1, column 2]

Parts:
C1, C3, C5, C7, C9, C11, C13, C15, C17, C19, C21, C23, C25, C27, C29, C31, C33, C35, C37, C39, C41, C43, C45, C47, C49, C51, C53, C55, C57, C59, C61, C63: 4.7µF; C_0603
C2, C4, C6, C8, C10, C12, C14, C16, C18, C20, C22, C24, C26, C28, C30, C32, C34, C36, C38, C40, C42, C44, C46, C48, C50, C52, C54, C56, C58, C60, C62, C64: 100nF; C_0603
C82: 1µF; C_0603
J1, J2, J3, J4, J5, J6, J7, J8, J9, J10, J11, J12, J13, J14, J15, J16, J17, J18, J19, J20, J21, J22, J23, J24, J25, J26, J27, J28, J29, J30, J31, J32, J33, J34, J35, J36, J37, J38, J39, J40, J41, J42, J43, J44, J45, J46, J47, J48, J49, J50, J51, J52, J53, J54, J55, J56, J57, J58, J59, J60, J61, J62, J63, J64: MSO-P1040H07T; TDR_MSO-P1040H07T
P1, P2, P3, P4, P5, P6, P7, P8: PH2-16-UA; PinHEADER_2x08_P2.54mm_Vertical
U1, U2, U3, U4, U5, U6, U7, U8, U9, U10, U11, U12, U13, U14, U15, U16, U17, U18, U19, U20, U21, U22, U23, U24, U25, U26, U27, U28, U29, U30, U31, U32: MIC4127; IC_MSOP-8_3x3mm_P0.65_EP_1.95x2.15_TV

Connections:
1: P1.1, U1.2 (IN_A)
2: P1.3, U1.4 (IN_B)
3: P2.1, U2.2 (IN_A)
4: P2.3, U2.4 (IN_B)
5: P3.1, U3.2 (IN_A)
6: P3.3, U3.4 (IN_B)
7: P4.1, U4.2 (IN_A)
8: P4.3, U4.4 (IN_B)
9: P1.5, U5.2 (IN_A)
10: P1.7, U5.4 (IN_B)
11: P2.5, U6.2 (IN_A)
12: P2.7, U6.4 (IN_B)
13: P3.5, U7.2 (IN_A)
14: P3.7, U7.4 (IN_B)
15: P4.5, U8.2 (IN_A)
16: P4.7, U8.4 (IN_B)
17: P1.9, U9.2 (IN_A)
18: P1.11, U9.4 (IN_B)
19: P2.9, U10.2 (IN_A)
20: P2.11, U10.4 (IN_B)
21: P3.9, U11.2 (IN_A)
22: P3.11, U11.4 (IN_B)
23: P4.9, U12.2 (IN_A)
24: P4.11, U12.4 (IN_B)
25: P1.13, U13.2 (IN_A)
26: P1.15, U13.4 (IN_B)
27: P2.13, U14.2 (IN_A)
28: P2.15, U14.4 (IN_B)
29: P3.13, U15.2 (IN_A)
30: P3.15, U15.4 (IN_B)
31: P4.13, U16.2 (IN_A)
32: P4.15, U16.4 (IN_B)
33: P5.1, U17.2 (IN_A)
34: P5.3, U17.4 (IN_B)
35: P6.1, U18.2 (IN_A)
36: P6.3, U18.4 (IN_B)
37: P7.1, U19.2 (IN_A)
38: P7.3, U19.4 (IN_B)
39: P8.1, U20.2 (IN_A)
40: P8.3, U20.4 (IN_B)
41: P5.5, U21.2 (IN_A)
42: P5.7, U21.4 (IN_B)
43: P6.5, U22.2 (IN_A)
44: P6.7, U22.4 (IN_B)
45: P7.5, U23.2 (IN_A)
46: P7.7, U23.4 (IN_B)
47: P8.5, U24.2 (IN_A)
48: P8.7, U24.4 (IN_B)
49: P5.9, U25.2 (IN_A)
50: P5.11, U25.4 (IN_B)
51: P6.9, U26.2 (IN_A)
52: P6.11, U26.4 (IN_B)
53: P7.9, U27.2 (IN_A)
54: P7.11, U27.4 (IN_B)
55: P8.9, U28.2 (IN_A)
56: P8.11, U28.4 (IN_B)
57: P5.13, U29.2 (IN_A)
58: P5.15, U29.4 (IN_B)
59: P6.13, U30.2 (IN_A)
60: P6.15, U30.4 (IN_B)
61: P7.13, U31.2 (IN_A)
62: P7.15, U31.4 (IN_B)
63: P8.13, U32.2 (IN_A)
64: P8.15, U32.4 (IN_B)
DIGPOT_SCL: P8.6
DIGPOT_SDA: P8.2
FAN_DRIVE: P5.4
FAN_PWM: P5.16
FAN_TACHO: P5.12
NTC: P5.8
unnamed: C1.1, C2.1, U1.6 (V+)
unnamed: C1.2, C2.2
unnamed: C3.1, C4.1, U2.6 (V+)
unnamed: C3.2, C4.2
unnamed: C5.1, C6.1, U3.6 (V+)
unnamed: C5.2, C6.2
unnamed: C7.1, C8.1, U4.6 (V+)
unnamed: C7.2, C8.2
unnamed: C9.1, C10.1, U5.6 (V+)
unnamed: C9.2, C10.2
unnamed: C11.1, C12.1, U6.6 (V+)
unnamed: C11.2, C12.2
unnamed: C13.1, C14.1, U7.6 (V+)
unnamed: C13.2, C14.2
unnamed: C15.1, C16.1, U8.6 (V+)
unnamed: C15.2, C16.2
unnamed: C17.1, C18.1, U9.6 (V+)
unnamed: C17.2, C18.2
unnamed: C19.1, C20.1, U10.6 (V+)
unnamed: C19.2, C20.2
unnamed: C21.1, C22.1, U11.6 (V+)
unnamed: C21.2, C22.2
unnamed: C23.1, C24.1, U12.6 (V+)
unnamed: C23.2, C24.2
unnamed: C25.1, C26.1, U13.6 (V+)
unnamed: C25.2, C26.2
unnamed: C27.1, C28.1, U14.6 (V+)
unnamed: C27.2, C28.2
unnamed: C29.1, C30.1, U15.6 (V+)
unnamed: C29.2, C30.2
unnamed: C31.1, C32.1, U16.6 (V+)
unnamed: C31.2, C32.2
unnamed: C33.1, C34.1, U17.6 (V+)
unnamed: C33.2, C34.2
unnamed: C35.1, C36.1, U18.6 (V+)
unnamed: C35.2, C36.2
unnamed: C37.1, C38.1, U19.6 (V+)
unnamed: C37.2, C38.2
unnamed: C39.1, C40.1, U20.6 (V+)
unnamed: C39.2, C40.2
unnamed: C41.1, C42.1, U21.6 (V+)
unnamed: C41.2, C42.2
unnamed: C43.1, C44.1, U22.6 (V+)
unnamed: C43.2, C44.2
unnamed: C45.1, C46.1, U23.6 (V+)
unnamed: C45.2, C46.2
unnamed: C47.1, C48.1, U24.6 (V+)
unnamed: C47.2, C48.2
unnamed: C49.1, C50.1, U25.6 (V+)
unnamed: C49.2, C50.2
unnamed: C51.1, C52.1, U26.6 (V+)
unnamed: C51.2, C52.2
unnamed: C53.1, C54.1, U27.6 (V+)
unnamed: C53.2, C54.2
unnamed: C55.1, C56.1, U28.6 (V+)
unnamed: C55.2, C56.2
unnamed: C57.1, C58.1, U29.6 (V+)
unnamed: C57.2, C58.2
unnamed: C59.1, C60.1, U30.6 (V+)
unnamed: C59.2, C60.2
unnamed: C61.1, C62.1, U31.6 (V+)
unnamed: C61.2, C62.2
unnamed: C63.1, C64.1, U32.6 (V+)
unnamed: C63.2, C64.2
unnamed: C82.1, P8.10
unnamed: J1.1, U1.7 (~OUT_A)
unnamed: J2.1, U1.5 (~OUT_B)
unnamed: J3.1, U2.7 (~OUT_A)
unnamed: J4.1, U2.5 (~OUT_B)
unnamed: J5.1, U3.7 (~OUT_A)
unnamed: J6.1, U3.5 (~OUT_B)
unnamed: J7.1, U4.7 (~OUT_A)
unnamed: J8.1, U4.5 (~OUT_B)
unnamed: J9.1, U5.7 (~OUT_A)
unnamed: J10.1, U5.5 (~OUT_B)
unnamed: J11.1, U6.7 (~OUT_A)
unnamed: J12.1, U6.5 (~OUT_B)
unnamed: J13.1, U7.7 (~OUT_A)
unnamed: J14.1, U7.5 (~OUT_B)
unnamed: J15.1, U8.7 (~OUT_A)
unnamed: J16.1, U8.5 (~OUT_B)
unnamed: J17.1, U9.7 (~OUT_A)
unnamed: J18.1, U9.5 (~OUT_B)
unnamed: J19.1, U10.7 (~OUT_A)
unnamed: J20.1, U10.5 (~OUT_B)
unnamed: J21.1, U11.7 (~OUT_A)
unnamed: J22.1, U11.5 (~OUT_B)
unnamed: J23.1, U12.7 (~OUT_A)
unnamed: J24.1, U12.5 (~OUT_B)
unnamed: J25.1, U13.7 (~OUT_A)
unnamed: J26.1, U13.5 (~OUT_B)
unnamed: J27.1, U14.7 (~OUT_A)
unnamed: J28.1, U14.5 (~OUT_B)
unnamed: J29.1, U15.7 (~OUT_A)
unnamed: J30.1, U15.5 (~OUT_B)
unnamed: J31.1, U16.7 (~OUT_A)
unnamed: J32.1, U16.5 (~OUT_B)
unnamed: J33.1, U17.7 (~OUT_A)
unnamed: J34.1, U17.5 (~OUT_B)
unnamed: J35.1, U18.7 (~OUT_A)
unnamed: J36.1, U18.5 (~OUT_B)
unnamed: J37.1, U19.7 (~OUT_A)
unnamed: J38.1, U19.5 (~OUT_B)
unnamed: J39.1, U20.7 (~OUT_A)
unnamed: J40.1, U20.5 (~OUT_B)
unnamed: J41.1, U21.7 (~OUT_A)
unnamed: J42.1, U21.5 (~OUT_B)
unnamed: J43.1, U22.7 (~OUT_A)
unnamed: J44.1, U22.5 (~OUT_B)
unnamed: J45.1, U23.7 (~OUT_A)
unnamed: J46.1, U23.5 (~OUT_B)
unnamed: J47.1, U24.7 (~OUT_A)
unnamed: J48.1, U24.5 (~OUT_B)
unnamed: J49.1, U25.7 (~OUT_A)
unnamed: J50.1, U25.5 (~OUT_B)
unnamed: J51.1, U26.7 (~OUT_A)
unnamed: J52.1, U26.5 (~OUT_B)
unnamed: J53.1, U27.7 (~OUT_A)
unnamed: J54.1, U27.5 (~OUT_B)
unnamed: J55.1, U28.7 (~OUT_A)
unnamed: J56.1, U28.5 (~OUT_B)
unnamed: J57.1, U29.7 (~OUT_A)
unnamed: J58.1, U29.5 (~OUT_B)
unnamed: J59.1, U30.7 (~OUT_A)
unnamed: J60.1, U30.5 (~OUT_B)
unnamed: J61.1, U31.7 (~OUT_A)
unnamed: J62.1, U31.5 (~OUT_B)
unnamed: J63.1, U32.7 (~OUT_A)
unnamed: J64.1, U32.5 (~OUT_B)
unnamed: P1.2, P1.4, P1.6, P1.8, P1.10, P1.12, P1.14, P1.16
unnamed: P2.2, P2.4, P2.6, P2.8, P2.10, P2.12
unnamed: P2.14, P2.16
unnamed: P3.2, P3.4, P3.6, P3.8, P3.10, P3.12, P3.14, P3.16
unnamed: P4.2, P4.4, P4.6, P4.8, P4.10, P4.14
unnamed: P5.2, P5.6, P5.10, P5.14
unnamed: P6.2, P6.4, P6.6, P6.8, P6.10, P6.12, P6.14, P6.16
unnamed: P7.2, P7.4, P7.6, P7.8, P7.10, P7.12, P7.14, P7.16
unnamed: P8.4, P8.8, P8.12, P8.14, P8.16
unnamed: U1.3 (GND), U1.9 (PAD)
unnamed: U2.3 (GND), U2.9 (PAD)
unnamed: U3.3 (GND), U3.9 (PAD)
unnamed: U4.3 (GND), U4.9 (PAD)
unnamed: U5.3 (GND), U5.9 (PAD)
unnamed: U6.3 (GND), U6.9 (PAD)
unnamed: U7.3 (GND), U7.9 (PAD)
unnamed: U8.3 (GND), U8.9 (PAD)
unnamed: U9.3 (GND), U9.9 (PAD)
unnamed: U10.3 (GND), U10.9 (PAD)
unnamed: U11.3 (GND), U11.9 (PAD)
unnamed: U12.3 (GND), U12.9 (PAD)
unnamed: U13.3 (GND), U13.9 (PAD)
unnamed: U14.3 (GND), U14.9 (PAD)
unnamed: U15.3 (GND), U15.9 (PAD)
unnamed: U16.3 (GND), U16.9 (PAD)
unnamed: U17.3 (GND), U17.9 (PAD)
unnamed: U18.3 (GND), U18.9 (PAD)
unnamed: U19.3 (GND), U19.9 (PAD)
unnamed: U20.3 (GND), U20.9 (PAD)
unnamed: U21.3 (GND), U21.9 (PAD)
unnamed: U22.3 (GND), U22.9 (PAD)
unnamed: U23.3 (GND), U23.9 (PAD)
unnamed: U24.3 (GND), U24.9 (PAD)
unnamed: U25.3 (GND), U25.9 (PAD)
unnamed: U26.3 (GND), U26.9 (PAD)
unnamed: U27.3 (GND), U27.9 (PAD)
unnamed: U28.3 (GND), U28.9 (PAD)
unnamed: U29.3 (GND), U29.9 (PAD)
unnamed: U30.3 (GND), U30.9 (PAD)
unnamed: U31.3 (GND), U31.9 (PAD)
unnamed: U32.3 (GND), U32.9 (PAD)
OE: P4.12
TX_ACTIVE: P4.16

Notes on the sheet:
ALL BYPASS CAPACITORS MUST BE RATED FOR A MINIMUM OF 25V, AND PREFFERABLY DERATED 2x
Switcher feedback to control board This cap must be >20V tolerant
I2C from control board for digipot
Driver PCB - Drive section
Logic power input from controller board
MISC. signals from control board
